birdybro/FPGA_Amp/TASKS.md

# Engineering task ledger

Last updated: 2026-08-15

## Current milestone

Advance the openly routed V1 phono core toward a stereo product-board platform
without changing the frozen reference circuit. The product architecture now
includes a separately clocked eARC/ARC TV input, touchscreen front panel,
premium physical controls, motor-follow volume, line conversion, and independent
power/protection. The Nexys Video artifact remains ready for volatile SRAM
loading; matching connected hardware and an installed open programmer are still
external blockers. Product eARC work is additionally gated by adopter/vendor
access and finished-device compliance.

## Active, highest value first

- [x] Implement the board-facing relay/XSMT sequence for the routed DAC PCB.
  Normal release asserts `LINE_RELAY_EN_CTL`, waits 491,520 fabric clocks
  (5 ms at 98.304 MHz), then asserts `DAC_SOFT_UNMUTE_CTL`; orderly mute drops
  XSMT first, waits the same conservative interval, and then opens the relays.
  Emergency mute drops both controller permissions on the next fabric edge,
  while the PCB's independent `HARD_MUTE_N` remains the asynchronous veto.
  Directed RTL covers release, orderly mute, release cancellation, and
  emergency drop. Yosys reports 28 estimated XC7 logic cells / 22 flip-flops /
  no DSP or BRAM / zero warnings. Physical relay/ramp/transient timing remains
  a bench release gate.
- [x] Integrate PCM5242 initialization, verification, and runtime health into
  one fail-low controller. The verifier cannot start before all 20 writes are
  ACKed; the first four-register runtime poll cannot start before all 24
  page/read/status checks pass; and `unmute_permitted` stays low until all 48
  transactions succeed. Periodic polls then check live/latched clock errors,
  active/sticky output shorts, DSP boot, and run state. Simulation proves
  success, ACK-only and startup-snapshot non-permission, both startup failure
  phases, and post-unmute short detection that revokes permission. Yosys reports
  340 estimated XC7 logic cells / 439 flip-flops / no DSP or BRAM / zero
  warnings. Top-level pin integration and physical fault/mute timing remain
  release gates.
- [x] Add a synthesizable one-byte-register I2C read primitive needed by the
  PCM5242 verification layer. The engine emits address+W, register, repeated
  START, address+R, one data byte, master NACK, and STOP while honoring clock
  stretching. Its bus-level regression checks all three transmitted bytes,
  returned data, released-bus completion, and fail-closed address-NACK abort.
  Yosys reports 70 estimated XC7 logic cells / 63 flip-flops / no DSP or BRAM /
  zero warnings. This primitive does not itself declare the DAC configured;
  the completed verifier/controller layers own that decision.
- [x] Implement the PCM5242 write-only reference-path bootstrap. The common I2C
  engine now supports one- or two-byte register addresses without regressing
  the ADAU1761 path. The new sequence emits twenty exact transactions at board
  address 0x4c for external SCK, 24-bit I2S, direct stereo routing, ROM
  interpolation program 1, unity digital/analog gain, VREF output, no
  de-emphasis, and disabled zero-detect auto mute. A bus model checks every
  byte, released-bus completion, and fail-closed NACK abort. Yosys reports 83
  estimated XC7 logic cells / 86 flip-flops / no DSP or BRAM / zero warnings.
  `configuration_written` is explicitly not an unmute permit; the downstream
  verifier and runtime monitor now provide the stronger controller gate.
- [x] Generate and openly route the four-layer PCM5242 DAC/line-output Rev-A
  EVT board. The 112 x 72 mm design implements 48 kHz external-clock slave I2S,
  I2C unity/reference configuration, separate analog/digital TPS7A2033
  post-regulation, official-reference 499 ohm balanced and RCA reconstruction
  branches, three normally-open fail-open signal relays, and provisional
  chassis-referenced ESD sites. Two SN74LVC1G08 gates independently require
  controller and external-supervisor permission before relay drive or PCM5242
  XSMT can assert; all permissions fail low. Rotating the DAC to face its analog
  pins toward the filters fixed the initially fragile output escapes. The open
  route has 581 segments and 86 vias; KiCad 10.0.5 reports zero ERC, zero DRC,
  and zero unconnected items. The verifier locks converter/interlock/relay pad
  maps, mode straps, filter values, DNP chassis options, loading calculations,
  stack, dimensions, and routing minima. This is not fabrication-released:
  register/readback firmware, loaded audio and mute/brownout measurements,
  connector/chassis mechanics, ESD/RF, stackup, DFM, and physical validation
  remain gates.
- [x] Generate and openly route the four-layer phono/ADC Rev-A EVT board. The
  130 x 90 mm design implements 47.5 kilohm MM loading, relay-selected
  0/47/100/147 pF capacitance, OPA1656 flat 20.008/26.064/32.002 dB gain,
  OPA1632 fully differential drive/filtering, a 48 kHz master PCM4202 with its
  reference-mode HPF disabled, local +/-12 V/+5 V/+3.3 V post-regulation,
  fail-low relay controls, separated relay power, and a chassis-bond population
  choice. The open Freerouting route has 926 segments and 141 vias; KiCad 10.0.5
  reports zero ERC, zero DRC, and zero unconnected items. A source-aware verifier
  locks pad maps, relay defaults, straps, headroom calculations, stack,
  dimensions, DNP states, and routing minima. This is not fabrication-released:
  production RCA/ground mechanics, measured capacitance/noise/hum/overload/
  crosstalk/RF/ESD, stackup review, muted switching, and the 128-fS FPGA receive
  path remain gates.
- [x] Generate and openly route the six-layer front-panel controller Rev-A EVT
  board. Its STM32H753ZIT6 allocation machine-checks 106 unique LQFP-144 I/Os
  for RGB565 LTDC, 32 MiB x16 SDRAM, 32 MiB Quad-SPI, capacitive touch, three
  panel encoders, mute/standby, digital-board control, and the motor-volume
  daughterboard. The board also implements the TPS62132 3.3 V rail, TPS61165
  nominal 60.2 mA backlight boost, MCU analog/core power, oscillators, reset,
  SWD, source damping, fail-asserted mute, and separate panel/control/motor
  harnesses. KiCad 10.0.5 reports 0 ERC, 0 DRC, and 0 unconnected items on the
  150 x 90 mm route with 1,827 segments and 327 vias. Exact project-local Molex
  54104-4031/52271-0679 footprints now reproduce the manufacturer-drawing pad
  count, pitch, land size, contact style, and fitting-nail geometry under
  regression. This is not a fabrication release: physical connector fit/FAI,
  six-layer stackup/SI and SDRAM timing, switching-supply layout, enclosure
  mechanics, sourcing, EMC, and physical validation remain gates. The pin audit
  also proves direct RMII Ethernet is unavailable in this Rev-A LQFP allocation.
- [x] Create and openly route the first KiCad EVT PCB for the motorized-volume
  subsystem. The 80 x 48 mm four-layer daughterboard implements the protected
  5 V rail, DRV8874 PH/EN bridge, hardware current regulation, IPROPI and fault
  telemetry, separate motor and dual-position connectors, ratiometric wiper
  filtering, DNP snubber site, and eight labeled test points. One source table
  generates its native schematic, PCB placement, custom symbols, and BOM;
  Freerouting v2.2.4 supplies the checked-in route through DSN/SES. KiCad 10.0.5
  reports 0 ERC, 0 DRC, and 0 unconnected items, and a source-aware verifier
  checks the DRV8874 pin map, board dimensions, stack, DNP state, connector
  isolation, minimum geometries, and reports. Gerbers, split drill files, maps,
  report, and DNP-filtered placement data regenerate with
  `make kicad-motor-fab`. This is an unbuilt motor-only EVT board; connector
  release, thermal-via strategy, motor emissions, stall thresholds, mechanism
  feel, and life qualification remain open.
- [x] Establish a comprehensive product hardware baseline for eARC, LCD/touch,
  premium physical controls, and motorized volume. The architecture partitions
  the product into digital/eARC, phono/ADC, DAC/line-output, front-panel, and
  power/protection boards so motor/display/HDMI currents are physically
  separated from the MM input. Fifty-two classified requirements and 31 signal
  rows across six board interfaces are machine checked. Mutation regressions
  reject duplicate IDs, unknown boards, untraced requirements, connector-contact
  overcommit, interface-budget drift, or downgrading the reference, stereo-PCM,
  analog-mute, and motor-out-of-audio-path invariants. This is a board
  architecture/specification result, not a released schematic, BOM, eARC
  license, compliance result, or motor-life claim.
- [x] Implement the mechanism-independent motor-volume servo core in portable
  C11. It provides soft endpoint clamping, far/approach duty, deadband/coast,
  exact reversal dead time, explicit and inferred manual takeover, hardware-
  current-feedback stall retention, travel timeout, driver/sensor faults, and a
  safe clear that adopts present position instead of retrying a stop. The first
  host run exposed and fixed a pending-reversal/manual-takeover collision; the
  failing reversal sequence is retained. The warning-as-error regression now
  passes. This does not validate PWM/ADC peripherals, motor EMI/torque/noise,
  touchscreen interaction, or mechanism lifetime.
- [x] Implement the matching stereo FPGA master-volume endpoint outside the
  historical model. Unsigned Q0.31 targets slew in at most 1,024 valid samples
  by default without division; zero and the exact-unity sentinel bypass
  multiplication, while signed stereo products retain all 64 bits and use
  symmetric round-to-nearest. Warning-free directed/randomized RTL covers
  retargeting, rounding, stereo independence, silence, unity, and invalid-target
  retention. Yosys reports 312 estimated logic cells / 151 flip-flops / eight
  DSP48E1 / no BRAM / zero problems. The primitive is not yet wired into the
  mono Nexys top, and this is no placed timing or stereo product-fit claim.
- [ ] Close eARC EVT-0 gates before a mainboard schematic: confirm the current
  supported audio-device receiver/successor and supply path; obtain HDMI adopter
  and vendor reference/API access; compare SRC4392 and AD1896 with asynchronous
  PCM; verify stereo LPCM capability exchange, ARC fallback, CEC volume, mute,
  relock, and latency on analyzer/EVM hardware. Do not advertise compressed or
  multichannel formats in V1.
- [x] Add PCM5242 page-aware register readback and startup status verification.
  Twenty-four exact operations select pages 0/1, compare every critical field
  with reserved-bit-safe masks, return to page 0, and require detected 48 kHz,
  512-fS SCK, 64-fS BCK, valid-clock flags, DSP boot, and run state. Directed
  bus simulation proves success plus masked-mismatch and NACK fail-closed paths.
  Yosys reports 170 estimated XC7 logic cells / 173 flip-flops / no DSP or BRAM /
  zero warnings. `configuration_verified` remains distinct from the earlier
  ACK-only result and is a startup snapshot; the integrated controller now
  follows it with continuous clock/short/power polling before and after unmute.
- [ ] Turn the completed front-panel controller and motor-volume EVT boards
  into a fabrication candidate: print/fit the drawing-derived Molex footprints,
  obtain assembler DFM and first-article inspection; obtain a fabricator stackup
  and run SDRAM/LTDC/clock SI; manually review and refine both switching
  converters; freeze encoder/display/enclosure geometry; select keyed production
  harnesses; then close sourcing, EMC, touch-safety, motor torque/noise/stall,
  and 100,000-cycle mechanism qualification.
- [x] Extend and verify the I2S receive boundary for the phono board's PCM4202
  master mode: 24-bit data in 64-BCK half-frames at 128-fS/6.144 MHz BCK and
  48 kHz LRCK. The receive-only block crosses complete stereo frames into
  49.152 MHz fabric through a depth-8 asynchronous FIFO so it does not force a
  future 32-BCK DAC onto the ADC clock. Both 32- and 64-BCK protocol regressions
  pass; the exact PCM4202 test passes 16 frames with unrelated phase,
  backpressure, held-valid checks, signed endpoints, and injected LRCK fault.
  Yosys reports 252 LC / 791 FF / no DSP or BRAM / zero structural problems.
  Physical FPGA-pin timing and populated-board validation remain open.
- [ ] Implement and openly route the actual stereo product hierarchy before
  freezing the production FPGA/package. The present 217-DSP mono Nexys build is
  evidence for an XC7A200T resource-class baseline, not proof that stereo plus
  TV routing, delay, diagnostics, and future full-amplifier headroom fit or meet
  timing/thermal limits.

- [x] Close the remaining 49.152 MHz complete-stream timing gap with registered
  cross-block scheduling, guided by the now-completed legal route. Circular
  histories reduce the complete 384 kHz candidate from 17,693 LC / 14,737
  packed FFX to 15,716 LC / 8,589 packed FFX. The full A200T route reaches
  48.482 MHz versus 49.152 MHz, leaving a 1.38% gap; its 20.626 ns state-to-
  tube path crosses the corrected/current voltage mux, plate-node subtraction,
  Q20 conversion, and factorized-tube input mapping. Exact acceptance/chord
  tube-pin prefetch removes that path, and a diagnostic-only four-boundary KCL
  maximum pipeline preserves all KCL/solver/stream vectors at 127 clocks, but
  the clean legal route reaches only 47.07 MHz through chord preview and tube
  conversion. Reject this pin-prefetch/deep-maximum family: another pin register
  costs a clock per correction pass and cannot fit the 127-of-128-clock
  contract. A zero-latency
  late selector now converts the current/corrected stage-one pin pairs in
  parallel and moves the mux onto the two 32-bit tube buses. It preserves the
  64-output/512-update stream exactly at 127 clocks and improves the best legal
  seed-1 route to 48.700 MHz, a remaining 0.92% miss; seed 2 routes at 45.051
  MHz and seed-3 routing was bounded after two unusually expensive iterations.
  Its critical path is now the exact KCL residual-maximum diagnostic. A new
  low-state sideband scans the nine stable rows with one comparator in eight
  clocks, matches 1,024 BE + 1,024 trapezoidal KCL vectors and the complete
  stream, and cuts the pack to 54,699 LUTX / 8,657 FFX / 4,044 CARRY4 / 207
  DSP. Its legal 14-iteration route reaches only 47.567 MHz because the
  corrected-node-to-tube path becomes critical again. Registering the six exact
  one-cycle-early chord nodes, while leaving subtraction and Q-format conversion
  in the existing preview-to-launch interval, preserves the complete stream at
  127 clocks and closes the open A200T route at 61.072 MHz against 49.152 MHz.
  Yosys measures 15,220 LC / 8,855 FF / 207 DSP / 10 RAMB18 equivalents; open
  packing measures 54,280 LUTX / 8,855 FFX / 3,979 CARRY4 / 207 DSP. The legal
  23-iteration seed-1 route has a 16.37 ns terminal-current/state path with
  6.44 ns logic and 9.94 ns routing, leaving 3.97 ns positive estimated slack.
  Seed 2 also closes in 14 iterations at 51.080 MHz with a 19.58 ns
  registered-node-to-tube path and 0.77 ns positive estimated slack.
  This is timing closure under nextpnr's experimental `DEFAULT` grade, not
  qualified XC7A200T-1 signoff or hardware validation; bitstream generation is
  verified separately below.
  Do not replicate the prior four-boundary implementation, whose 1,076 added
  registers made routing pathological. A
  broad 123-clock parallel/pipelined profile remains exact but
  grows to 242 DSP / 66,658 packed LUTX and places at only 39.62 MHz, so do not
  promote it. Lower resource occupancy or nominal cycle margin alone is not
  timing closure.
- [ ] Complete physical implementation evidence for the selected A200T timing
  profile. The seed-1/seed-2 routes are retained, and a new fully open
  Project-X-Ray conversion now reproducibly turns the selected 44,258,864-byte
  FASM into 20,230 frame records and a 9,730,907-byte `.bit`. Two conversions
  produce the same SHA-256 (`98a53adf...2b9dcb`) after repository-relative
  source metadata and a fixed epoch timestamp; `bitread -C` validates 24,060
  configuration frames / 2,432,650 words. Run the physical oscillator/signature
  smoke test when matching hardware is available. Keep the experimental
  `DEFAULT` timing estimate distinct from qualified speed-grade and board
  measurements.
- [x] Implement and openly route the exact Nexys Video audio-clock source.
  Cascade two XC7 MMCMs from the real R4 100 MHz oscillator to 12.288 MHz
  codec MCLK and 49.152 MHz fabric clocks, with exact 960/614.4 MHz VCOs.
  Check the ratios and 128 fabric clocks per 384 kHz sample from RTL in Python.
  With an explicit 10 ns input constraint, nextpnr derives both generated
  domains and completes routing in three iterations; the 24-bit activity
  counter reaches 291.55 MHz against its correct 49.152 MHz constraint under
  the experimental `DEFAULT` grade. Pack use is 99 LUTX / 24 FFX / 6 CARRY4 /
  2 BUFG / 2 MMCM. The open Project-X-Ray stage emits a CRC-readable
  9,730,853-byte bitstream at SHA-256 `1d7d934f...234b248`. The arithmetic
  contract also checks that physical G4 `CPU_RESETN` is inverted before the
  active-high MMCM reset; this fixes and supersedes the prior
  `941a8c07...e0ff656` artifact, whose reset polarity was wrong. This is a
  clock-only harness, not hardware frequency measurement or codec operation.
- [x] Implement the board serial-clock and reset-release leaf. Divide the exact
  49.152 MHz fabric clock by 16 to 3.072 MHz BCLK, promote only this external
  interface clock through an XC7 BUFG, and keep sample processing on the fabric
  clock plus enables. Assert fabric/I2S resets asynchronously but release them
  through separate three-edge owning-domain synchronizers. A warning-free RTL
  test checks exact 16-clock periods, release latency, and asynchronous
  reassertion. Yosys reports 10 FDCE / 1 CARRY4 / 1 BUFG, zero problems, and no
  warnings. Full named-board timing awaits composition with the pin top.
- [x] Implement the device-neutral open-drain I2C register-write primitive for
  codec startup. It transmits the seven-bit device address, 16-bit register
  address, and one data byte, honors SCL clock stretching, samples every ACK,
  and completes with a STOP after either ACK or NACK. A directed bus-target
  test checks exact bytes, a deliberate address-byte NACK, and recovery on the
  next write. Warning-free Yosys XC7 synthesis reports 43 estimated logic
  cells, 59 flip-flops, three CARRY4s, and no DSP or BRAM. Reads, arbitration,
  multi-main operation, and codec register readback remain explicitly out of
  scope.
- [x] Add and verify the ADAU1761-specific fail-closed startup sequence. Keep
  the codec subordinate to FPGA-supplied BCLK/LRCLK, configure direct 12.288
  MHz MCLK for the 48 kHz family, leave the line outputs muted until the last
  writes, and abort before later writes on any NACK. The bus-target regression
  checks all 27 address/register/data transactions and then injects a NACK at
  table index five, where the sequencer exposes the failure and emits no more
  writes. Warning-free Yosys XC7 synthesis reports 88 estimated logic cells,
  94 flip-flops, ten CARRY4s, and no DSP/BRAM. Physical ACKs and analog output
  behavior remain unmeasured.
- [x] Compose and structurally verify the actual Nexys Video pin top: the exact
  clock leaf, reset/BCLK leaf, codec initializer, single shared LRCLK,
  bidirectional serial audio, calibrated 384 kHz phono hierarchy, SPI control,
  forced-zero startup data, and status indicators. A mutation-tested contract
  checks 18 physical pin/IO-standard pairs, active-low reset, open-drain I2C,
  the internal 3.072 MHz BCLK constraint, the selected 384 kHz schedule, and
  fail-closed release. The shared-I2S guard regression proves zero DAC data and
  a held serial-transport reset until two synchronized ready edges, preventing
  undefined pre-bootstrap ADC frames from filling the receive FIFO. Complete
  Yosys synthesis reports 16,688
  LC / 11,687 FF / 217 DSP / ten RAMB18 equivalents with zero structural
  problems; open packing uses 59,710 LUTX / 11,687 FFX / 4,192 CARRY4. This is
  composition/fit evidence, not a hardware-ready claim.
- [x] Complete and retain the full board route, then generate and CRC-check its
  Project-X-Ray bitstream. Both generated domains and the otherwise-uninferrable
  fabric-divided BCLK carry explicit constraints. Static placement estimates
  only 41.03 MHz, but router2 reaches zero overuse in 20 iterations and passes
  at 54.663 MHz against 49.152 MHz fabric plus 123.457 MHz against 3.072 MHz
  BCLK under the experimental `DEFAULT` grade. The 56,556,532-byte routed FASM
  converts to 20,230 frame records and a 9,730,825-byte `.bit`; two conversions
  are identical at SHA-256 `5f196e52...b09dbb8`, and `bitread -C` accepts
  24,060 frames / 2,432,650 words. The result is neither qualified -1 timing
  nor a hardware validation claim; the image remains unprogrammed.
- [ ] Program the complete image on a matching Nexys Video and validate reset,
  12.288 MHz MCLK, 3.072 MHz BCLK, 48 kHz LRCLK, all codec I2C ACKs, startup
  silence, line-output audio, and SPI diagnostics with external instruments.
  The non-programming preflight now validates the exact part, byte count,
  SHA-256, CRC evidence, frame count, and word count before using the official
  openFPGALoader `nexysVideo` detection profile. It passes the artifact but the
  2026-08-15 host has neither openFPGALoader nor a Nexys Video USB device, so
  no configuration was attempted. `nexys-audio-program-sram` is deliberately
  volatile-only and requires successful detection first. Do not infer any of
  these physical results from the CRC-readable artifact.
- [x] Carry the timing-closed 384 kHz / 49.152 MHz profile into the actual
  fabric adapter and complete SPI-controlled I²S hierarchy. Preserve 768 kHz
  as the default, add explicit rate-selectable vector/test runners, and pass
  exact adapter, serial I²S, register-control, and 15-frame SPI regressions.
  The 384 kHz pin test accepts all 64 serial inputs, matches 44 observable DAC
  frames, keeps each local FIFO high-water mark at one, and measures 265 fabric
  clocks from model input to output-valid plus the unchanged 192-BCLK/three-
  sample frame-boundary latency. Yosys reports 15,699 LC / 9,085 FF for the
  adapter and 16,614 LC / 11,586 FF for the full SPI/I²S top, both with
  217 DSP / 10 RAMB18 equivalents and zero structural-check problems. A board
  top now has a real, openly routed 49.152 MHz/12.288 MHz clock source. It
  is now composed with the codec's physical shared LRCLK, deterministic reset
  release, and byte-tested ADAU1761 initialization in the board wrapper. Full
  board routing and all physical codec/audio behavior remain unvalidated; do
  not label the clock-only image or structural board top as hardware-ready.
- [ ] Isolate and reduce the remaining fixed circuit/state/chord error. With
  the implemented 1,024-point grid branch, raw final-window error is now
  0.372/0.291 mV at 1.0 V and 0.631/0.321 mV at 1.5 V for backward Euler/
  trapezoidal. A continuous-coefficient fixed-interface A/B bounds integer tube
  evaluation to <=0.168 mV burst RMS and identifies circuit/state/chord as the
  6.40--19.07 mV dominant burst layer. The implemented terminal correction
  cuts 1.0/1.5 V burst RMS to 4.895/6.817 mV for backward Euler and
  4.709/3.604 mV for trapezoidal at 127 clocks. Held-bank reselection,
  rational terminal relaxation, full dual-triode operating points, and
  stage-one-split banks all fail cross-level/recovery acceptance. Further
  contraction now requires a different solver formulation or additional
  schedule margin; do not tune the frozen circuit or accept a one-level fit.
- [ ] Prove 98.304 MHz named-part timing for the 127-clock trapezoidal terminal
  stream. Current controlled generic synthesis fits XC7A100T structurally at
  18,280 LC / 206 of
  240 DSP48E1 / 8 RAMB18E1 + 1 RAMB36E1, but the parallel terminal-current path and one-clock
  sample margin require the open Yosys/nextpnr-Himbaechel place/route flow
  before hardware selection. Project X-Ray contains the exact
  `xc7a100tcsg324-1` part, but the current experimental backend uses a single
  `DEFAULT` timing grade, so routing evidence and qualified -1 speed-grade
  signoff must remain distinct. The first full-solver harness packs at 50,789
  `SLICE_LUTX` / 174 DSP and reaches only 13.90 MHz after placement. A
  value-only tube substitution places at 13.67 MHz, falsifying the hypothesis
  that Hermite is the dominant whole-solver limiter. A standalone bit-exact
  iterative Hermite replacement now
  closes post-route at 132.54 MHz with two DSPs and three-clock latency, but
  inserting that latency into all three dependent tube functions would exceed
  the current 127-clock solver budget. The separately named value-only linear
  candidate instead retains eight clocks: 100,000-point error is 47.49 nA
  worst, tube and complete terminal solver RTL are bit-exact, and the isolated
  tube routes at 113.24 MHz. Its full harness packs at 49,530 `SLICE_LUTX`, 166
  DSP, 13 RAMB18E1, and 5 RAMB36E1. The isolated 54-DSP terminal-current block
  improves from 51.95 to 88.83 MHz when its exact overflow count is balanced,
  but still misses 98.304 MHz. Isolated chord routes at 46.40 MHz and isolated
  KCL routes at 16.64 MHz, with KCL's accumulator-to-global-fallback cone
  matching the whole-solver failure. A bit-exact residual staging register and
  balanced KCL reductions retain the 127-clock integrated contract and improve
  KCL placement to 33.92 MHz. Parallel evaluation of the two physical tube
  sections is bit-exact at 84/95 clocks and fits structurally at 209/240 DSPs.
  The recovered margin now funds two KCL column-fill clocks, two KCL finish
  clocks, and two chord-apply clocks per pass: the complete solver is exact at
  119 clocks and the chord route closes at 100.92 MHz. A legal 42.07 MHz KCL
  route instead identified the exact maximum diagnostic as the limiter.
  Accumulator and final-only maximum pipelines plus exact sign-extension fit
  tests now produce a bit-exact 126-clock complete schedule and raise the
  isolated KCL to 92.23 MHz post-route. Close the remaining 6.6% KCL gap and
  resolve the full-hierarchy congestion: the 14,990-LC design packs to 59,027
  slice LUT elements / 209 DSPs but places at only 34.20 MHz. Region analysis
  shows KCL and terminal-current spanning nearly all DSP rows while the two
  tube engines and chord occupy separated hard-block regions. The same netlist
  uses only 209/740 DSPs on XC7A200T, but seed/default placement reaches 23.83
  MHz, a second seed reaches 30.55 MHz, and timing-weight-20 reaches only 35.22
  MHz. Capacity alone is therefore rejected as the fix. A selectable two-batch
  terminal-current schedule now proves 1,027 standalone and 512 integrated
  vectors exact at 127 clocks, cuts DSP use from 209 to 189, and routes its
  isolated block at 90.50 MHz with the default weight and 99.59 MHz with timing
  weight 20, closing that block's constraint. The complete hierarchy
  nevertheless places at only 25.02 MHz with 59,514 LUTX / 14,590 FFX, worse
  than baseline. Timing weight 20 raises the complete candidate only to 32.56
  MHz and disperses its 34 terminal DSPs across a 91-by-167 coordinate region;
  it remains slower than the selected baseline's 34.20 MHz. Resource sharing
  in one block and placer-weight tuning are therefore both insufficient. An
  overlapping hierarchy floorplan improves the candidate to 36.83 MHz by
  reserving left/center DSP columns for KCL/RHS and center/right columns for
  nonlinear blocks, but still misses by 2.67x. Mapping all eleven KCL
  multipliers to LUT logic is legal but grows the complete candidate to
  101,479/126,800 packed LUT elements while reducing DSPs to 117; the isolated
  71,592-LUT block does not complete analytical placement in a useful interval,
  so no Fmax is claimed. Softening only the two capacitor multipliers reduces
  the full design to 171 DSPs at 66,341 LUTX, but the isolated KCL places at
  only 37.57 MHz and is also rejected. Decoupling the final-only exact maximum
  diagnostic recovers a bit-exact 123-clock schedule and five-clock margin.
  Acceptance-edge branch-9 prefetch now spends none of that margin while
  sharing the two KCL capacitor products: isolated/full DSP use falls from
  72/209 to 63/200, but placement reaches only 72.95/35.06 MHz and a weight-20
  full placement falls to 29.05 MHz. Composing this with terminal-current
  sharing produces an exact 124-clock, 180-DSP solver, but default and
  floorplanned placements reach only 30.63/32.94 MHz. Develop a broader
  cross-block time-multiplexed schedule with registered multiplier boundaries;
  do not treat lower DSP occupancy by itself as evidence of timing progress.
  A separately labeled 384 kHz/8x study now bounds 10/20 kHz SPICE error at
  0.06653 dB / 0.02234 degree and finds complete-circuit selected products
  within 0.52 dB of 768 kHz through steady 0.5 V, while exposing an 11.33 dB
  static-tube stress penalty at -118.65 dBc. Its 256-cycle budget is promising,
  but reference mode remains 16x. Distinct 384 kHz fixed assets and the
  nonlinear RTL core are now exact across 1,024 all-bank chord, 1,024 KCL, and
  512 persistent solver vectors at 10/11/127 clocks with zero solver diagnostics. The 19-bit chord bank
  costs nine more DSPs than the controlled 768 kHz core synthesis. The complete
  48→384→48 kHz candidate is now exact for 64 external outputs / 512
  nonlinear updates with zero diagnostics. After serial center-tap sharing and
  reset-masked circular resampler histories, full-stream synthesis is 15,716
  LC / 8,547 FF / 207 DSP / 10 RAMB18 equivalents at 384 kHz and 16,062 / 9,033
  / 206 / 10 at 768 kHz. The
  772,608-update fixed transient comparison is diagnostic-clean and finds only
  +0.1875 ms recovery delta / -84.71 dB aligned recovery error. Known-delay
  windowed-sinc alignment measures the pop at -35.92 dB overall / 2.623 mV
  peak / -53.33 dB in-band; this supersedes a flawed linear-interpolation
  result. Converter/float/fixed in-band decomposition is -67.49/-55.71/-53.33
  dB. Long-vector RTL proves both
  rate-specific implementations exact for 24,576 outputs / 294,912 nonlinear
  updates. The matched absolute pop-response comparison now measures -61.47 dB
  residual / 0.539 mV maximum at the 384 kHz path's 48 kHz output versus
  -61.00 dB / 0.546 mV for 768 kHz, without latency, gain, or DC fitting and
  with zero failed solves. Thus this transient does not favor 16x. The complete
  harness packs on A100T but heap placement fails legalization; a legal A200T
  static placement reaches only 34.40 MHz against 98.304 MHz. An explicit
  49.152 MHz schedule is exact with one clock of solver margin and improves
  static placement to 38.34 MHz against 49.152 MHz, but still misses by 1.28x.
  Circular decimator history removes 4,173 packed FFX and makes heap placement
  legal for the first time, although its 22.79 MHz estimate still fails the
  clock. Circular interpolation then improves static placement to 41.27 MHz
  while preserving every stream output. Reference mode remains 16x and broader
  registered scheduling is required.

## Completed this milestone

- [x] Implement and route exact tube-pin prefetch plus diagnostic-only KCL
  maximum retiming without changing the 127-clock solver schedule. Match 1,024
  backward-Euler KCL, 1,024 rate-specific trapezoidal KCL, 512 persistent
  solver, and 64-output/512-update complete-stream vectors. Remove the
  invalid-only combinational maximum load identified by route. Measure 15,852
  LC / 9,793 FF / 207 DSP / 10 RAMB18 equivalents and a legal 47.07 MHz A200T
  route with a 21.24 ns chord-preview/tube-input path. Reject the candidate as
  slower than the selected 48.482 MHz baseline.

- [x] Route the circular-resampler 49.152 MHz complete-stream harness legally
  on XC7A200T. Measure 48.482 MHz post-route, a 1.38% miss, with 56,041 LUTX /
  8,589 FFX / 4,116 CARRY4 / 207 DSP and a 20.626 ns state/voltage/tube-input
  critical path. Preserve the generated FASM only as implementation evidence;
  do not claim a bitstream or hardware readiness. Compose and reject a broader
  exact 123-clock profile after its 66,658-LUTX / 242-DSP A200T placement
  reaches only 39.62 MHz.

- [x] Replace reset-cleared half-band interpolator shift registers with reset-
  masked circular distributed memories using one multiplexed asynchronous read
  port for MAC and pre-write odd-phase capture. Add a reset-after-history test
  for both output phases and preserve all unit, 8x/16x converter, and complete
  stream vectors exactly. Measure 364 LC / 306 FF / 4 DSP for one stage, 950 /
  938 / 12 for 8x, and 1,417 / 1,229 / 16 for 16x. Reduce complete 384/768 kHz
  synthesis to 15,716 / 16,062 LC and static A200T placement to 56,041 LUTX /
  8,589 FFX / 4,116 CARRY4 / 207 DSP at 41.27 MHz versus 49.152 MHz.

- [x] Replace reset-cleared half-band decimator shift registers with a
  reset-masked circular distributed-memory history. Mask retained memory using
  an explicit valid-sample count, add a post-history reset regression, and
  preserve every unit, 8x/16x converter, and complete 384/768 kHz stream output
  exactly. Measure 349 LC / 214 FF / 4 DSP for one 79-tap stage, 961 / 618 / 12
  for 8x, and 1,408 / 817 / 16 for 16x. Reduce the complete 384 kHz stream to
  16,315 LC / 10,520 FF / 207 DSP and prove legal A200T heap placement at
  58,363 packed LUTX / 10,562 FFX, while retaining its failed 22.79 MHz timing
  result and the static placer's still-failing 38.38 MHz result, then skip
  routing. The refreshed static hierarchy is 2,725 LUTX / 618 FFX / 12 DSP for
  the decimator versus the prior 8,397 / 4,791 / 12.

- [x] Extend the placed-JSON hierarchy analyzer to distinguish the complete
  8x interpolator and decimator, with regression coverage for flattened names.
  Measure decimator/interpolator/KCL placement at 8,397/5,193/19,609 LUTX,
  4,791/2,910/2,920 FFX, and 244x143/244x139/190x185 coordinate spans.

- [x] Implement and verify a half-frequency fabric schedule for the 384 kHz
  candidate without changing circuit arithmetic. Match both 1,024-output
  interpolator schedules and all 64 complete outputs / 512 nonlinear updates
  exactly at 49.152 MHz with zero diagnostics and a 127-of-128-clock solver.
  Place the complete A200T static design at 38.34 MHz versus 49.152 MHz and
  retain the reduced-netlist heap legalization failure; do not claim routing.

- [x] Serialize the half-band decimator center tap through the existing MAC.
  Preserve the pre-shift history operand explicitly and match 256 unit, both
  8x/16x chain, and both complete nonlinear-stream regressions exactly. Reduce
  decimator synthesis from 24 to 12 DSPs at 8x and from 32 to 16 at 16x; update
  complete synthesis to 17,693 LC / 207 DSP and 18,280 / 206 respectively.

- [x] Add a complete 384 kHz three-pin timing harness and open-tool placement
  path. Pack it on XC7A100T at 63,902 LUTX / 14,737 FFX / 4,071 CARRY4 / 207
  DSP; retain the failed heap legalization. Legally place the same netlist on
  XC7A200T with the static placer and measure 34.40 MHz versus 98.304 MHz, then
  skip routing after the 2.86x miss.

- [x] Compare both floating rate-specific pop/control responses directly with
  ngspice driven at the ideal INPUT node. Use matched interpolation and
  decimation, 180,000--360,000 raw SPICE points per run, and no alignment or
  gain fitting. Measure -61.47/-61.00 dB external residual and 0.539/0.546 mV
  maximum error at 384/768 kHz, with zero failed Newton solves.

- [x] Correct the transient A/B alignment error. Add optional caller-known
  latency and 64-tap Lanczos-windowed sinc interpolation to the null tool, with
  a three-tone upper-band regression below -70 dB. Re-run 772,608 fixed updates
  and a 393,216-update converter/float/fixed decomposition. Supersede the
  invalid -15.18 dB / 85.6 mV pop claim with -35.92 dB overall / 2.623 mV peak /
  -53.33 dB in-band; measure recovery at -84.71 dB overall.

- [x] Capture the rate-study transients directly from both complete RTL paths.
  Match 4,096 pop plus 8,192 overload/recovery outputs at each rate: 24,576
  Q8.24 outputs / 294,912 nonlinear updates are fixed-exact with zero
  diagnostics at 127 clocks. Bound maximum solver residual to 0.672 uA at
  384 kHz and 0.322 uA at 768 kHz; retain the separate failing rate A/B.

- [x] Compare complete 384/768 kHz fixed streams on matched record-pop and
  accepted-range 0.5 V overload/control trajectories. Process 772,608 nonlinear
  updates with zero diagnostics; measure 147.771/147.583 ms recovery. The
  original linear-interpolation null was later corrected by the explicit
  known-delay/windowed-sinc milestone above.

- [x] Compose the exact three-stage converters with the rate-specific 384 kHz
  banked-terminal core. Generalize the bit-accurate stream model and vector/
  RTL runners without changing the 768 kHz default; match 64 outputs across
  512 persistent nonlinear updates with zero converter, solver, or deadline
  diagnostics. The initial controlled Yosys structures were 17,629 LC / 219 DSP
  / 10 RAMB18 equivalents for 384 kHz and 18,302 / 222 / 10 for 768 kHz;
  center-tap multiplier sharing supersedes those resource values above.

- [x] Implement an explicit three-stage 48↔384 kHz converter without changing
  the four-stage reference modules. Match 1,024 interpolation and 128
  decimation Q8.24 RTL outputs exactly with zero saturation, overrun, or input-
  phase errors; measure eight internal samples / 20.83 µs of interpolation
  scheduling delay. The initial decimator was 2,355 LC / 24 DSP; the later
  bit-exact center-tap sharing milestone supersedes it with 2,448 / 12.

- [x] Generate a distinct 384 kHz trapezoidal fixed-point asset set and make
  its numerical differences explicit. Widen the Q17.1 chord bank from signed
  18 to 19 bits for its measured -23,414..+146,717 range; preserve exact
  product width/sign extension. Match 1,024 all-bank chord, 1,024 KCL, and 512
  persistent full-solver RTL vectors at 10/11/127 clocks with zero solver diagnostics. Synthesize the
  complete core using Yosys at 13,713 LC / 183 DSP / 10 RAMB18 equivalents,
  versus a controlled 13,158 / 174 / 10 build at 768 kHz; make no Fmax or
  reference-mode promotion claim.

- [x] Quantify an explicit 8x internal-rate architecture without changing the
  16x reference. Extend the reproducible SPICE study to 384 kHz trapezoidal,
  add static-Koren and complete-circuit 8x/16x nonlinear product comparisons at
  20 kHz, and retain exact 10 ms coherent analysis windows. Measure -0.058 dB
  complete-circuit fundamental change, <=0.52 dB selected-product change
  through steady 0.5 V, and the separate -118.65 dBc static-tube stress result.
  Record the remaining fixed/RTL/transient verification debt rather than
  silently reducing oversampling.

- [x] Reuse the two KCL capacitor products through one explicit 48-by-44-bit
  multiplier. Prefetch branch 9 on the accepting edge so 1,024 vectors per
  integration method remain exact at 16 clocks and the 512-vector complete
  solver stays exact at 123 clocks. Measure 63 isolated and 200 complete DSPs,
  but only 72.95 and 35.06 MHz placement. Compose with terminal-current sharing
  at 124 clocks / 180 DSPs and measure only 30.63 MHz default and 32.94 MHz
  floorplanned placement. Retain the exact area option while rejecting it as
  the selected timing architecture.

- [x] Decouple the final-only exact KCL maximum diagnostic from the correction
  result consumed by chord. Verify 1,024 vectors per integration method and 512
  stateful solver vectors bit-exact; reduce correction latency from 19 to 16
  clocks and the full solver from 126 to 123. Measure a legal 87.07 MHz isolated
  route, an 80.03 MHz timing-weight-20 placement, and a 31.97 MHz full placement
  at 209 DSPs. Retain the recovered five-clock schedule margin while rejecting
  diagnostic decoupling itself as an Fmax or congestion fix.

- [x] Add an exact open-XC7 pack-only measurement stage and evaluate mapping
  all eleven KCL multipliers to LUT logic. Assert the multiplier selection in
  Yosys before remapping; measure isolated 71,592 LUTX / 0 DSP and complete
  101,479 LUTX / 117 DSP packing. Stop two non-convergent exploratory
  placements without claiming timing, retain normal pack summaries, and reject
  the all-soft mapping as the current A100T implementation.

- [x] Measure a narrower soft-multiplier split. Assert selection of only the
  two 48x44 capacitor multipliers while retaining nine DSP-backed matrix
  multipliers. Record 36,327 LUTX / 54 DSP and 37.57 MHz for isolated seed-2
  placement, versus the selected 72-DSP KCL's 92.23 MHz route; pack the full
  hierarchy at 66,341 LUTX / 171 DSP and reject further implementation work on
  an unpipelined soft-multiply branch.

- [x] Implement and measure two-batch terminal-current resource sharing. Use
  fixed lane-pair muxes to avoid synthesis-created variable-index trees, pass
  1,027 exact block vectors and 512 complete stateful vectors, and retain the
  exact 127-clock deadline. Measure 34 rather than 54 isolated DSPs, 90.50 MHz
  with the default placement weight, and 99.59 MHz with timing weight 20. Then
  measure the complete 189-DSP hierarchy at only 25.02 MHz placement. Keep the
  implementation selectable and reject it as the default full-solver timing
  fix rather than reporting an isolated-only resource/timing win.

- [x] Preserve open-XC7 tuning experiments with validated, filesystem-safe run
  tags. Reproduce the isolated timing-weight-20 closure in its own artifact
  directory, then place the complete shared-terminal solver at the same weight.
  Measure only 32.56 MHz versus the 98.304 MHz target and retain the default
  25.02 MHz evidence separately.

- [x] Add and measure a nextpnr pre-place hierarchy floorplan. Reject a strict
  76-of-80-DSP left partition after it fails to complete a first heap iteration;
  retain overlapping two-column regions with 80 sites of slack per group.
  Measure 36.83 MHz, 13.1% above the unconstrained weight-20 candidate but still
  2.67x short, and skip routing.

- [x] Extend the pinned nextpnr-Himbaechel bootstrap and device-qualified runner
  to XC7A200T, add a Nexys Video timing-only harness, and place the unchanged
  complete solver. Measure 28% DSP and 21% packed-LUT occupancy, then test two
  seeds and a doubled heap timing weight. The best 35.22 MHz estimate remains
  2.79x short, so skip routing and reject larger-device capacity alone rather
  than claiming the 209/740-DSP fit solves timing.

- [x] Add a placement-only open-XC7 stage that emits separate placed netlist,
  log, report, and summary artifacts without claiming routing. Add a flattened
  placed-JSON hierarchy analyzer. Reproduce the complete 126-clock candidate at
  34.20 MHz placement with 59,027 LUTX / 13,458 FFX / 4,036 CARRY4 / 209 DSP /
  20 RAMB18 equivalents, then stop before routing because the miss is 2.87x.
  Quantify the KCL/terminal/tube/chord hard-block dispersion instead of
  extrapolating the isolated 92.23 MHz KCL result.

- [x] Use legal route evidence to pipeline the KCL accumulator and only the
  consumed final maximum-residual diagnostic. Preserve 1,024 vectors in each
  integration mode and 512 complete stateful vectors, including all 48 format
  fallbacks and 18 correction saturations. Replace generic signed-25 bounds
  compares with the exact sign-extension predicate; improve isolated KCL
  post-route timing from 42.07 through 64.90/72.31 to 92.23 MHz. Measure the
  complete exact schedule at 126 clocks and 14,990 LC / 13,458 FF / 209 DSP /
  20 RAMB18 equivalents without claiming full-hierarchy closure.

- [x] Add selectable bit-exact timing boundaries to the KCL column/finish and
  chord apply paths. Preserve 1,024 vectors in each KCL integration mode, 1,024
  chord vectors, the unchanged default latencies, and 512 complete stateful
  terminal vectors. Measure the combined schedule at 119 clocks, the chord at
  100.92 MHz post-route, and the KCL at only 38.95 MHz after placement. Record
  the remaining KCL miss instead of claiming whole-solver closure.

- [x] Add a selectable parallel dual-triode schedule without changing either
  physical operating point or arithmetic. Preserve 512-vector backward-Euler
  and complete trapezoidal/banked/terminal state and diagnostics exactly;
  reduce measured latency from 116/127 to 84/95 clocks. Add a named open-flow
  harness and measure 15,887 LC / 7,360 FF / 209 DSP / 20 RAMB18-equivalents,
  leaving 31 DSPs and 33 clocks per internal sample for timing work.
- [x] Isolate the actual network timing hierarchy. Measure chord correction at
  46.40 MHz and the original KCL engine at 16.64 MHz post-route. Capture
  capacitor 9 early, stage the final residual in the existing second-tube wait
  window, and balance cross-row fit/max/saturation reductions. Preserve 1,024
  backward-Euler, 1,024 trapezoidal, and 512 terminal-solver exact vectors;
  retain 127 integrated clocks while improving KCL placement to 33.92 MHz.
- [x] Factor the ten terminal trapezoidal current recomputations into a
  bit-exact timing unit, preserve both 512-vector solver regressions at 116/127
  clocks, and add named-part terminal/KCL/chord harnesses. Measure 54 DSPs and
  51.95 MHz for the original serial overflow count, replace it with an exact
  balanced popcount, and improve isolated post-route timing to 88.83 MHz.

- [x] Implement and independently label the value-only factorized timing
  candidate. Reproduce its 1,024/8,192/4,096 tables; measure 47.49 nA worst
  static current error; pass 4,110 tube, 512 wide-solver, and 512 complete
  terminal-solver vectors at unchanged latency; compare five circuit levels
  against Hermite and analytical full Newton; route the isolated tube at
  113.24 MHz. Do not promote it until the complete route is measured.
- [x] Break the three-dependent-multiply cubic-Hermite path into a reusable,
  bit-exact iterative kernel. Verify 4,096 full-range vectors, reset, and a
  start-while-busy transition; preserve all 4,110 factorized-tube vectors;
  measure 265 LC / 2 DSP structurally and 132.54 MHz after named-part routing.
  Keep its experimental `DEFAULT` timing grade and unintegrated cycle cost
  explicit.
- [x] Bound the oversampled SPI transport under arbitrary asynchronous raw-pin,
  response, and clear activity. Prove 11 synchronizer, bit-count, request,
  response-state, saturating-frame-count, frame-reset, and sticky-precedence
  properties through 32 fabric clocks; separately reach request decode,
  short-frame, and response-underflow paths in 100 steps. Keep the eight-frame
  directed integration as byte-order/full-frame evidence and do not claim
  unbounded induction or a placed SCLK limit.
- [x] Exhaustively prove converter-boundary arithmetic/control safety. Cover
  the valid positive input-coefficient range before the explicit signed-32
  cast, exact registered valid/output/hold behavior, output PCM endpoint
  saturation, and both saturating counters/sticky-clear transitions in 12
  assertions under arbitrary full-width samples and coefficients. Close Yosys
  SAT temporal induction at depth 2 and reach endpoint, saturation, and both
  invalid-configuration paths without replacing the Python bit-exact vectors.
- [x] Bound the asynchronous BCLK-rate monitor that drives the modern
  fail-closed mute guard. In a reduced four-clock/two-window instance, prove 16
  exact BCLK binary/Gray, synchronizer, window, delta, lock/drop, saturation,
  and sticky-clear properties for every 32-step arbitrary-clock interleaving.
  Reach lock followed by a retained bad-rate state in 48 steps. Keep physical
  clock accuracy, synchronizer placement/metastability, stopped-clock liveness,
  and the production 1,024-edge ratio as separately verified claims.
- [x] Bound the low-rate diagnostic-clear toggle CDC under arbitrary clock
  levels and a protocol assumption that the preceding event is observed before
  another launches. Prove ten exact pipeline, pulse-width, outstanding-event,
  no-fabrication, and accounting properties through 40 global steps; reach two
  delivered events. Add directed evidence that destination reset with an odd
  retained source toggle replays the idempotent command, and document that this
  primitive is not a reset-independent or arbitrary-rate event channel.
- [x] Bound the coherent held-bus CDC snapshot under arbitrary source and
  destination clock levels after disciplined shared startup reset. Prove nine
  capture provenance, hold stability, exact-data, valid-pulse, accounting, and
  idle properties through 40 global steps, then find a nonzero complete-transfer
  witness. Keep the result explicitly bounded and retain the directed
  destination-reset-during-request RTL test because mid-transaction reset is
  outside the formal environment.
- [x] Formally prove deterministic frame scheduling under arbitrary source
  validity/data and diagnostic clear. Use nine assertions for phase wrap,
  ready/valid/present launch strobes, accepted data, zero fill, and the exact
  saturating 32-bit underflow transition. Close Yosys 0.66 SAT temporal
  induction at depth 2 and reach an absent boundary followed by a present one.
- [x] Formally prove the atomic converter-calibration guard. Under arbitrary
  candidates, valid, mute, and clear inputs after reset, require exact
  acknowledge, simultaneous pair commit, rejection immutability, sticky
  accumulation, and clear precedence in 12 assertions. Close Yosys 0.66 SAT
  temporal induction at depth 2 and find one invalid-reject/commit/unsafe-reject
  witness. This covers the guard, not the upstream host transport.
- [x] Add a sound bounded multi-clock formal environment around the asynchronous
  FIFO. After a shared reset asserted on local edges and released while clocks
  are low, leave both clock levels and all controls arbitrary. Prove 13 Gray,
  blocked-pointer, occupancy/watermark, valid, and sticky-fault properties for
  every 32-step interleaving; separately reach depth four and both illegal-side
  stickies in 24 steps. Keep unbounded induction explicitly open because the
  current invariant set does not close it.
- [x] Formally verify the single-clock modern output mute/ramp control contract.
  With arbitrary post-reset data and controls, prove 15 reset, force-clamp,
  valid, hold, exact gain-transition, endpoint, monotonicity, and status
  assertions by Yosys 0.66 SAT temporal induction at depth 2. Separately find a
  non-vacuous witness reaching unity gain after four accepted samples. Package
  both checks as `make formal-mute`; the result does not claim CDC or analog
  speaker-safety coverage.
- [x] Integrate coherent I²S-domain FIFO diagnostics into the atomic register
  snapshot. Delay image/sequence commit until the held-bus CDC returns, expose
  busy/available status, pack RX/TX level and high-water nibbles at `0x35`, and
  make a 131,072-clock timeout retain the old image/sequence with sticky
  evidence. Prove normal capture, busy rejection, stopped-BCLK timeout,
  recovery/re-arm, timeout snapshot, and explicit clear; update the host client
  to poll completion and reject stale sequence results. Bump the compatible ABI
  minor to 1.1. Current structural synthesis is 354 LC / 735 FF for the register
  bank, 19,616 LC / 18,684 FF for the controlled hierarchy, and 19,719 LC /
  18,856 FF with SPI; the complete variants retain 216 DSP48E1 /
  8 RAMB18E1 + 1 RAMB36E1 and zero structural-check problems.
- [x] Implement the held-bus CDC primitive needed for coherent I²S-domain
  occupancy snapshots. Use a four-phase request/acknowledge protocol, hold all
  16 bits through two synchronizer stages plus a settling clock, re-arm safely,
  and survive destination reset during an active request. Prove three exact
  captures warning-free and synthesize to 5 LC / 75 FF / no DSP or RAM. The
  register transaction integration is recorded above.
- [x] Define the host-side SPI/register ABI in dependency-free Python. Encode
  exact ten-byte full-duplex frames, validate identity/version/capabilities and
  response status, require explicit mute ownership for snapshot/clear commands,
  and guard calibration commit/poll/sequence checks. Cover exact wire bytes,
  malformed/error responses, accepted/rejected calibration, and invalid host
  preconditions with six deterministic tests. A physical adapter backend remains
  a board task rather than part of the protocol contract.
- [x] Convert the measured BCLK-rate status into a fail-closed modern output
  policy at the register-controlled wrapper. Hold the immediate mute through
  three-window startup qualification, reassert it on stopped BCLK, retain it
  through clock reacquisition, snapshot the evidence, and release only after an
  explicit host clear reaches both fabric and I²S domains. Keep model scheduling
  active so startup qualification cannot overflow the receive FIFO. Updated
  later structural synthesis is 19,616 LC / 18,684 FF for the controlled
  hierarchy and 19,719 LC / 18,856 FF with SPI, both retaining 216 DSP48E1 /
  8 RAMB18E1 + 1 RAMB36E1 and zero structural-check problems.
- [x] Compose the SPI transport, fabric register bank, guarded calibration, and
  pin-facing I²S/model hierarchy. Prove 15 complete 5 MHz frames through the
  actual stack, including startup commit/readback, retained and refreshed
  force-mute snapshots, a snapshotted short-frame fault and transport count,
  and exactly one diagnostic clear in the unrelated BCLK domain. Synthesize the
  flattened hierarchy to
  19,719 LC / 18,856 FF / 216 DSP48E1 / 8 RAMB18E1 + 1 RAMB36E1 with zero
  structural-check problems; placed timing and a physical host backend remain
  open.
- [x] Implement an oversampled SPI mode-0 transport for the fabric register bus
  without a derived clock. Prove eight 80-bit transactions through the real
  register/calibration guard at 5 MHz, including identity read, calibration
  writes/commit/readback, bus-error status, short frame, withheld response,
  diagnostic clear, and saturating completion count. Synthesize warning-free to
  112 LC / 172 FF / no DSP or RAM. The complete composition is recorded above.
- [x] Integrate the fabric register bank around the pin-facing mono hierarchy.
  Freeze 20 fabric-coherent diagnostic words, synchronize four sticky I²S
  faults, transfer diagnostic clear by one toggle event, and own calibration/
  mute through the bus. Prove retained snapshots, startup calibration, and one
  I²S clear pulse across unrelated clocks; synthesize the crossing to 1 LC /
  5 FF and the complete wrapper to 19,616 LC / 18,684 FF / 216 DSP48E1 /
  8 RAMB18E1 + 1 RAMB36E1. No Fmax is claimed.
- [x] Implement a protocol-neutral fabric control register bank with reset-muted
  state, a coherent calibration shadow/commit transaction, distinct attempted
  and accepted sequences, retained rejection/bus errors, pulsed diagnostics
  clear, and atomic diagnostic snapshots. Prove accepted, invalid, unsafe,
  busy-write, bad-address, and snapshot-retention behavior warning-free;
  synthesize to 323 LC / 715 FF / no DSP or RAM. Pin and SPI integration are
  recorded above.
- [x] Test three schedule-neutral refinements to the remaining trapezoidal
  terminal error. Preserve exact negative results showing that within-sample
  bank reselection worsens 1.5 V/recovery, 5/4 residual relaxation improves
  burst error but displaces recovery state, and full dual-triode/stage-one-
  split Jacobian banks either fail cross-level validation or create 58
  residual-limit misses. Retain the production coefficients and schedule.

- [x] Implement and integrate a Gray-counter BCLK/fabric rate monitor. Require
  three consecutive 1,024 ± 1 edge windows for lock, drop lock and latch a bad
  window, reacquire after correction, clear retained evidence, detect a stopped
  BCLK as zero edges, and revoke live state on BCLK reset. The actual-rate pin
  test measures 1,024 edges across four
  windows without changing audio/latency. Synthesize standalone to 68 LC / 125
  FF and the updated pin top to 19,156 LC / 17,669 FF / 216 DSP48E1 /
  8 RAMB18E1 + 1 RAMB36E1.
- [x] Add conservative local-domain occupancy and retained high-water
  diagnostics to both sides of each asynchronous FIFO. Reach exact depth eight,
  drain to zero, clear watermarks, and preserve the 128-word wrap test. At the
  bridge, backpressure records RX 3/3 and TX 4/4 frames without loss; at the
  locked pin-level rate all four views peak at one frame without changing audio
  or latency. Updated synthesis is FIFO 127 LC / 331 FF, bridge 571 LC / 1,547
  FF, and the later clock-monitored pin top 19,156 LC / 17,669 FF; no DSP/RAM
  change from diagnostics.
- [x] Correct the pin-level integration clocks from the accidentally ratio-only
  100/3.125 MHz test to the stated 98.304/3.072 MHz rates. Timestamp internal
  handshakes and serial boundaries; gate the deterministic intervals and record
  192 BCLK / 62.500 us / 3.000 sample periods from the first complete ADC frame
  to the first complete valid model-output DAC frame. Keep this transport result
  separate from resampler/circuit and physical-converter group delay.
- [x] Compose the I²S/CDC bridge with the calibrated accuracy-first mono
  adapter. Under exactly frequency-locked 3.072/98.304 MHz clocks with unrelated
  phase, deliver all 64 serial stereo inputs to calibrated model state exactly,
  match all raw model outputs, and recover 45 consecutive observable DAC frames
  as exact mono duplicates. Retain expected startup starvation and zero all
  other diagnostics; atomically commit the startup converter-scaling pair while
  muted and reject a later live pair without changing active values; synthesize
  the later clock-monitored top to 19,156 LC / 17,669 FF /
  216 DSP48E1 /
  8 RAMB18E1 + 1 RAMB36E1 with no placed CDC/I/O/converter claim.
- [x] Add a protocol-neutral atomic calibration commit guard. Reset both active
  Q8.24 coefficients inactive, accept a positive pair only while fully muted,
  acknowledge the pair together, and preserve active values on invalid or live
  attempts with separate sticky diagnostics. Pass warning-free directed and
  pin-top regressions; synthesize the standalone guard to 14 LC / 67 FF / no
  DSP or RAM.
- [x] Compose the framed mono fabric datapath from scheduler through input
  calibration, exact trapezoidal/banked/terminal stream, output calibration,
  held ready/valid output, and explicit mono duplication. Match 64 calibrated
  inputs, raw model outputs, and PCM frames bit-for-bit under five clocks of
  output backpressure; force and clear one output overrun without overwriting
  the held frame while model/calibration diagnostics remain zero. Prevent the discovered hidden
  startup-state advance by holding the core reset through phase acquisition;
  integrate the downstream safety ramp and synthesize the combined hierarchy to
  18,642 LC / 16,354 FF / 216 DSP48E1 /
  8 RAMB18E1 + 1 RAMB36E1 with no structural problems and no timing claim.
- [x] Correct synthesis resource accounting to retain both RAMB18E1 and
  RAMB36E1 primitives plus their 18-Kib equivalent total. Existing factorized
  hierarchies use 8 RAMB18E1 + 1 RAMB36E1, not the formerly reported eight
  RAMB18E1-only count; numerical implementation is unchanged.
- [x] Align asynchronous-bridge frames to the solver's deterministic fabric
  schedule. Accept one held stereo frame per 2,048-clock period, prelaunch for
  one-clock calibration, inject zero on starvation, and retain a saturating
  underflow count. Verify phase zero and directed A/zero/B order warning-free;
  synthesize to 41 LC / 43 FF / no DSP or RAM.
- [x] Define and implement the converter calibration boundary without selecting
  hidden gain: PCM24 to input-referred Q8.24 volts and physical Q8.24 line volts
  to saturating PCM24. Match 4,159 Python/RTL vectors per direction with
  explicit endpoint, saturation, and invalid-coefficient diagnostics; synthesize
  to 95/86 LC, 66/58 FF, and 4 DSP48E1 per direction with no warnings.
- [x] Integrate the I²S protocol and CDC primitives into a bidirectional stereo
  frame bridge. Preserve 20 exact BCLK-to-fabric-to-BCLK frames under unrelated
  clocks and deliberate ready backpressure, verify owning-domain diagnostics,
  and synthesize the later instrumented hierarchy to 571 LC / 1,547 FF with zero
  structural problems and explicit register-expanded FIFO storage.
- [x] Implement conventional 24-bit stereo I²S in 32-BCLK slots. Loop 16 signed
  frames exactly through warning-free receive/transmit RTL; independently check
  32-period slots and delay bits; inject framing and underflow faults; synthesize
  RX/TX to 35/97 LC and 105/137 FF with no warnings or structural problems.
- [x] Implement a device-neutral dual-clock FIFO with Gray pointer crossings,
  two-flop synchronizers, registered read data, sticky overflow/underflow, and
  embedded formal invariants. Preserve directed and 128 wrapped words under
  unrelated clocks; with later occupancy watermarks, synthesize depth 8×32 to
  127 LC / 331 FF with zero
  structural problems and a documented register-expansion warning.
- [x] Add nine original, physically scaled PCM24 regressions covering silence,
  nominal/low-level THD, high-frequency intermodulation products, multitone,
  warp, pop, log sweep, and 1.5 V overload. Process 32,448 outputs / 519,168
  nonlinear updates with zero model diagnostics or WAV clips; measure
  0.019826%/0.011559% H2--H10 THD at 5/0.5 mV peak.
- [x] Extend the deterministic audio suite to 14 vectors / 69,440 external
  frames / 1,111,040 nonlinear updates. Add a 60 Hz/7 kHz, 4:1
  SMPTE-RP-120-style sideband profile (explicitly not an analyzer-conformance
  claim), a differential 5 mV one-sample impulse, and paired 250 ms nominal/
  0.5 V overload trajectories. With zero fixed diagnostics or WAV clips,
  measure 0.461295% profile IMD, a strictly causal 34-sample impulse onset and
  138.118 mV peak, and 147.750 ms 10%-nominal recovery relative to the input
  burst stop.
- [x] Add dependency-free 16/24/32-bit PCM WAV I/O, explicit peak-voltage
  scaling through the exact fixed V1 stream, and transparent latency/gain/
  fractional-delay null tooling. Run a 1,024-frame terminal-trapezoidal audio
  regression with zero diagnostics/clips, exact recovery of an injected
  23-sample delay, and separate +2.405/-30.462/-100.810 dB raw/latency/gain
  residuals.
- [x] Capture the complete trapezoidal terminal stream at 100 Hz, 1 kHz,
  10 kHz, and 20 kHz for 4,800 outputs each. Prove fixed/RTL identity and zero
  diagnostics; bound gain/phase error to 0.000134 dB / 0.000444 degree; and
  separate the 87.89 uV worst fitted startup drift from the -74.79 dB
  detrended waveform null.
- [x] Implement trapezoidal terminal correction with exact corrected Q4.44
  capacitor-current commit on the final chord edge. Match all state across
  384,000 overload updates with zero diagnostics; reduce 1.0/1.5 V burst RMS
  error to 4.709/3.604 mV; carry it through 64 complete-stream outputs; and
  synthesize the then-current 127-clock solver/stream to 14,945/20,241 LC,
  174/222 DSP48E1, and 8 RAMB18E1 + 1 RAMB36E1. Later controlled builds are
  recorded separately rather than rewriting this historical milestone.
- [x] Separate all 16 internal frequencies that fold to ±3 kHz in the captured
  complete-stream stress test. Prove the isolated 45 kHz third-harmonic output
  is exactly zero in Q8.24, capture the combined out-of-band projection exactly,
  and measure only a -176.96 dBc complete-vs-family-removed effect below fixed
  rounding closure; the nonfolded 3 kHz bin dominates by 102.37 dB.
- [x] Capture the banked terminal RTL through 384,000 control/overload updates
  at 20 mV, 0.5 V, 1.0 V, and 1.5 V. Preserve H1--H10, clipping asymmetry,
  grid current, recovery, and null metrics; prove full-state fixed equivalence
  and zero diagnostics while matching analytical burst THD within 0.00122
  percentage points and phase within 0.00221 degrees.
- [x] Carry the banked terminal solver through the complete mono resampling
  stream. Match 64 external outputs / 1,024 nonlinear updates exactly at the
  measured 127-clock solver latency with zero diagnostics, and synthesize the
  full hierarchy to 18,466 LC / 168 DSP48E1 / 8 RAMB18E1 + 1 RAMB36E1.
- [x] Implement the backward-Euler terminal correction in fixed Python and
  synthesizable RTL. Prove output/state identity to conventional four-pass,
  match 18,432 overload updates exactly at 127 clocks with zero diagnostics,
  and synthesize to 13,296 LC / 120 DSP48E1 / 8 RAMB18E1 + 1 RAMB36E1.
- [x] Sweep three through six corrections on the current banked solver for both
  integrators at 1.0/1.5 V over 100 ms. Measure fourth-pass burst improvement
  of 5.65--9.02 dB, six-pass residual <=0.207 uA, non-monotonic recovery-state
  error, and the rejected 145-clock minimum extra-pass projection.
- [x] Split integer tube evaluation from fixed circuit/state/chord error using
  the same Q24/Q20 input and Q31 current interfaces. Prove all intermediate
  banked runs diagnostic-clean; measure <=0.168 mV tube-evaluator burst error
  versus 6.40--19.07 mV circuit/state/chord error.
- [x] Decompose banked severe-overload error, sweep the grid-current table, and
  implement the selected 1,024-entry branch in fixed Python and RTL. Reduce
  direct worst error from 716 to 12.55 nA and 1.5 V final error from
  18.27/17.36 mV to 0.631/0.321 mV, preserve zero diagnostics, prove standalone
  and 36,864-state integrated RTL exactness, and retain eight mapped RAMB18E1s plus one RAMB36E1.
- [x] Add a Vgk-slew-qualified shallow bank for the severe cutoff arc. Preserve
  bit-exact <=1.0 V behavior, remove all 1.5 V residual-limit misses in both
  integration modes, prove 36,864 RTL states exact with every bank exercised,
  and retain the 116-clock schedule with no added DSP or block RAM.
- [x] Separate the factorized plate-law domain from its grid-current lookup.
  Prove every former 1.5 V range event was only `Vgk < -5 V`, expand plate-law
  acceptance to -8 V while retaining the -5 V grid leakage-floor clamp, and
  prove before/after audio bit-exactness. Exact integrated RTL now has zero
  arithmetic/range/fallback events at 1.5 V; the later slew-qualified bank
  closes the then-remaining 57/53 residual misses.
- [x] Tighten the shallow trapezoidal bank threshold from -2.50 to -2.75 V.
  Avoid every 0.5 V activation, retain zero 1.0 V failures and exact RTL, and
  reduce the final-window mean error from 1.042 to 0.537 mV.
- [x] Compare 100 ms banked waveforms against full Newton without alignment.
  At 1.0 V, improve raw burst error from -53.45/-53.65 dB to -76.43/-76.79 dB
  for backward Euler/trapezoidal; retain the trapezoidal 0.537 mV final-window
  mean error as an open selector/state discrepancy.
- [x] Implement integration-mode-specific cutoff-Jacobian banks in RTL; prove
  all 9,216 overload states per mode bit-exact, exercise every bank at the
  unchanged 116-clock latency, and synthesize without added DSP or block RAM.
- [x] Derive fixed cutoff-region Jacobian banks from the analytical stage-two
  trajectory. In the 100 ms Python gate, remove all 1.0 V residual failures in
  both integration modes without extra corrections, arithmetic/range events,
  or fallbacks; retain the separate 1.5 V residual limitation explicitly.
- [x] Prove wide RHS, backward-Euler/trapezoidal KCL, tube-stamp, and chord
  arithmetic bounds with conservative full-interface integer intervals. All 47
  checks pass; directed regressions cover the corrected 44-bit capacitor delta,
  34-bit `INT32_MIN` cathode-current sum, and saturating tube-pin conversion.
- [x] Establish repository engineering instructions and reproducible tool bootstrap.
- [x] Capture wide-solver RTL at 100 Hz, 1 kHz, 10 kHz, and 20 kHz; prove Q32
  fixed equivalence and <=0.0001943 dB / <=0.0009814 degree analytical error.
- [x] Capture 100 ms overload/recovery trajectories through 1.5 V; compare all
  state exactly and extend post-burst observation to 85 ms.
- [x] Capture the 16× decimator's cubic nonlinear alias trajectory; match 8,192
  outputs exactly and measure -137.814 dBc with zero saturation.
- [x] Integrate frame-aligned reset/warmup and the mute ramp around the wide
  stream; prove no state-reset sample escapes and synthesize the guarded top.
- [x] Compare 768 kHz backward Euler with SPICE at 100 Hz, 1 kHz, 10 kHz, and
  20 kHz; expose 4.72 degree high-frequency phase error and measure a floating
  trapezoidal candidate at <=0.0582 degrees for 10/20 kHz.
- [x] Compare 100 ms backward-Euler/trapezoidal overload trajectories through
  1.5 V; prove finite convergence and matched clean-region recovery.
- [x] Implement explicit fixed trapezoidal capacitor branches with Q30 voltage
  and signed Q4.44 previous-current history; pass the six-frequency nominal
  sweep with zero diagnostics.
- [x] Run fixed trapezoidal overload through 1.5 V; pass the <=0.5 V clean
  region, bound stored capacitor current, and expose the required 48-bit
  companion-conductance width.
- [x] Widen the KCL capacitor coefficient to signed 48-bit, add explicit
  previous/current-next ports, and pass 1,024 exact trapezoidal vectors without
  regressing the backward-Euler KCL.
- [x] Add persistent Q4.44 current state and a separate trapezoidal chord-
  inverse ROM to the selectable solver; match all 29 state words and diagnostics
  across 512 samples at 116 clocks and synthesize the hierarchy.
- [x] Carry trapezoidal state through the complete interpolator/solver/
  decimator stream; match 64 outputs / 1,024 internal updates with zero
  diagnostics and synthesize the selectable hierarchy.
- [x] Capture trapezoidal solver RTL at 100 Hz, 1 kHz, 10 kHz, and 20 kHz;
  prove complete fixed-state equivalence, nominal diagnostics, and bounded
  gain/phase error while linking the separate ngspice integration layer.
- [x] Capture the complete 48 kHz trapezoidal stream for 4,800 outputs at each
  of 100 Hz, 1 kHz, 10 kHz, and 20 kHz; prove exact fixed equivalence, zero
  diagnostics, and <=0.000111 dB / <=0.001185 degree error against the composed
  floating model. Measure the rate converters independently at exactly 51
  external samples / 1.0625 ms so their phase is not attributed to the circuit.
- [x] Extend floating trapezoidal overload observation to 235 ms after the
  burst. Measure 0.5 V 10%-nominal recovery at 146.552 ms, fit the coupled
  stage-two recovery modes at 98.2--118.1 ms, retain 1.0/1.5 V crossings as
  labeled projections, and record complete node/capacitor checkpoints.
- [x] Directly simulate nominal, 1.0 V, and 1.5 V floating trajectories through
  850 ms. Falsify the earlier single-exponential projection, measure 1.0 V
  sustained 10% recovery at 270.112 ms, and expose 413--451× late rebounds
  after opposing circuit modes temporarily cancel near 316--362 ms.
- [x] Capture selectable trapezoidal RTL through the accepted 0.5 V overload
  and 235 ms recovery window. Match 384,000 complete fixed-state updates with
  zero diagnostics and measure sustained 10% recovery at 146.570 ms, 18.23 µs
  from the independent floating trajectory.
- [x] Linearize the actual nine-node/tube circuit at DC and solve `det(G+sC)=0`
  without a generalized-eigenvalue dependency. Verify eight stable finite modes;
  identify 143.936 ms and 1.067763 s output-coupling modes that explain the
  overload cancellation/rebound and bound the next direct record at seven seconds.
- [x] Run seven-second nominal/1.0 V/1.5 V recovery trajectories. Measure all
  sustained 10%/1%/1 mV crossings through 6.371 s; validate the late two-pass
  chord handoff against Newton below 33.2 nV over 100 ms and 17.9 nV at the
  final-cycle probe, with zero solve failures.
- [x] Select, document, and version the Kennedy 1998 two-stage passive-RIAA circuit.
- [x] Implement AT-VM95E R/L/47.5 kΩ/150 pF cartridge loading.
- [x] Build ngspice DC, 10 Hz–100 kHz AC, transient, and 1 kHz H1–H10 level sweeps.
- [x] Verify nominal DC and quantify historical RIAA error without correcting it.
- [x] Implement canonical mathematical RIAA and regress against Bulletin E1.
- [x] Implement the Koren 12AX7 analytical/grid-current model and compare checked
  manufacturer-curve digitization.
- [x] Implement the 768 kHz nonlinear nodal/capacitor-state Python model and
  compare it with ngspice.
- [x] Characterize one through four Newton passes at 20 mV peak.
- [x] Reject raw linear-network fixed-point iteration and select three-pass
  quiescent-Jacobian chord iteration as the measured fixed/RTL candidate.
- [x] Implement reproducible 12AX7 tube LUTs, study four resolutions, and record
  mean/worst interpolation error.
- [x] Define tube-interface Q formats and a bit-accurate Python LUT model.
- [x] Define all V1 state/matrix/residual/inverse formats and implement an
  integer-only three-pass chord model with explicit rounding and saturation.
- [x] Decompose initial multitone error into tube-LUT and fixed-state/chord layers.
- [x] Design the four-stage 16× float/Q1.23-coefficient half-band reference,
  measure response/latency, and verify rejection of a nonlinear 45 kHz alias.
- [x] Implement the fixed Q8.24/Q1.23 per-stage MAC/rounding/saturation model and
  preserve the nonlinear alias test as a regression.
- [x] Reduce chord correction to DSP-native 18×25 operands; measure its error
  independently against the original Q17.15 × Q4.44 correction.
- [x] Implement, lint, synthesize, and verify the nine-node chord-correction RTL
  against 1,024 exact vectors including saturation boundaries.
- [x] Add CI jobs for Python/RTL/generated-asset regressions and ngspice/model
  cross-comparisons.
- [x] Implement synthesizable eight-clock 12AX7 RTL with range diagnostics.
- [x] Pass warning-free Verilator lint and 4,096 bit-exact randomized vectors.
- [x] Run generic XC7 synthesis and record actual structural resource use.
- [x] Implement exact capacitor-history RHS and heterogeneous-format KCL RTL;
  pass 1,024 vectors per block including residual saturation boundaries.
- [x] Integrate both 12AX7 halves, all ten capacitor branches, three corrections,
  final residual, state commit, and runtime diagnostics in a mono scheduler.
- [x] Match all nodes, capacitor states, output, residual, and counters for 512
  sequential fixed-model/RTL samples at a measured 126-clock latency.
- [x] Synthesize the complete hierarchy: 8,024 estimated XC7 logic cells,
  89 DSP48E1s, and 47 RAMB18E1s, with no structural check problems.
- [x] Implement serial-MAC half-band interpolator/decimator primitives and the
  complete 48↔768 kHz four-stage chains with saturation/overrun diagnostics.
- [x] Match 2,048 interpolation and 128 decimation stream outputs exactly;
  record the visible 18-internal-sample scheduler delay and structural resources.
- [x] Integrate the complete 48 kHz reference stream around the nonlinear solver,
  including saturating Q12.20-to-Q8.24 output conversion and diagnostics.
- [x] Match 64 consecutive end-to-end outputs / 1,024 nonlinear updates exactly;
  synthesize the full stream at 13,170 estimated LC, 137 DSP, and 47 RAMB18.
- [x] Sweep analytical and fixed behavior from 0.5 mV to 5 V at 1 kHz using the
  settled SPICE analysis window; quantify THD, compression, residual, and clips.
- [x] Measure low-level distortion at four larger LUT resolutions and reject a
  raw BRAM increase as an ineffective fix.
- [x] Implement and measure a fixed factorized Koren candidate using three
  value/slope 1-D LUTs with cubic Hermite interpolation: 51.8 nA worst current
  error and 0.0188% versus 0.0191% analytical THD at 5 mV.
- [x] Implement the standalone factorized tube RTL and pass 4,110 bit-exact
  randomized/boundary vectors at eight clocks, including five clip cases;
  after the grid-resolution implementation, synthesize at 1,496 LC,
  35 DSP48E1, and 8 RAMB18E1 + 1 RAMB36E1.
- [x] Integrate the factorized primitive as a selectable solver mode; match all
  state and diagnostics for 512 samples at 126 clocks and synthesize the full
  hierarchy at 9,148 LC, 108 DSP48E1, and 8 RAMB18E1 + 1 RAMB36E1.
- [x] Propagate factorized mode through the complete stream; match 64 outputs /
  1,024 circuit updates exactly with zero diagnostics and synthesize at 14,290
  LC, 156 DSP48E1, and 8 RAMB18E1 + 1 RAMB36E1.
- [x] Sweep 5 mV factorized fixed vs analytical at 20/50/100 Hz and
  1/10/20 kHz: ≤0.00846 dB gain error, ≤0.0729° phase error, and no diagnostic
  failures across 683,520 nonlinear samples.
- [x] Characterize 5 ms overload bursts at 20 mV, 0.5 V, 1.0 V, and 1.5 V,
  including peak grid current, clipping asymmetry, residual/range diagnostics,
  and recovery relative to an undisturbed nominal trajectory.
- [x] Sweep three through six chord corrections at 1.0/1.5 V; quantify residual,
  output error, range events, and the 126-to-213-clock serialized projection.
- [x] Run a 768,000-sample silence/bipolar-click state audit with node and all
  capacitor checkpoints; expose the Q12.20 deadband and preserve it as a
  reproducible regression rather than hiding it with output DC removal.
- [x] Implement a 40-bit Q28/Q32 node, Q30 history, branch-current Python
  candidate with staged Q30/Q34/Q40 correction precision. Reduce the click
  audit's late residual from 5.375 mV to 38.74 uV and the nominal 1 kHz raw null
  from -42.90 to -63.83 dB with zero diagnostics.
- [x] Sweep the wide-state candidate at 20/50/100 Hz and 1/10/20 kHz: bound
  gain/phase error to 0.000196 dB / 0.000982 degrees with zero diagnostics.
- [x] Re-run 20 mV--1.5 V overload with adaptive Q30/Q34/Q40 residual scaling:
  eliminate arithmetic saturation and improve clean-region recovery/error, but
  retain explicit 1.0/1.5 V convergence and 1.5 V range failures.
- [x] Implement the 40-bit Q28/Q32 chord corrector with bounded Q30/Q34/Q40
  scaling; match 1,024 vectors at ten clocks and synthesize to 1,701 XC7 logic
  cells / 9 DSP48E1 / no RAMB18. Reject the 5,531-cell arbitrary-shift version.
- [x] Implement two-clock wide RHS and ten-clock branch-current KCL blocks;
  match 1,024 vectors each with adaptive fallback, true overflow, and delayed
  tube-current coverage. Synthesize at 31 LC / 4 DSP and 8,034 LC / 72 DSP.
- [x] Integrate the wide factorized solver; match all 19 persistent states and
  diagnostics across 512 sequential samples at 116 clocks. Synthesize the
  hierarchy at 12,544 LC / 120 DSP48E1 / 8 RAMB18E1 + 1 RAMB36E1.
- [x] Integrate the wide solver into 16x interpolation/decimation; match 64
  outputs / 1,024 solves exactly with zero diagnostics and synthesize at 17,492
  LC / 168 DSP48E1 / 8 RAMB18E1 + 1 RAMB36E1.
- [x] Capture 23,040 wide-solver RTL samples at 5 mV/1 kHz; prove Q32 exactness
  and measure -0.000054 dB gain, -0.000187 degree phase, 0.019371% THD, and
  -63.834 dB raw residual directly from RTL output.
- [x] Implement and test a downstream Q0.16 output mute/ramp with reset-muted
  startup, symmetric rounding, exact-unity bypass, and synchronous fault clamp;
  synthesize at 171 XC7 logic cells, 2 DSP48E1s, and no block RAM.
- [x] Quantify flat/partial/full-analog RIAA front-end architectures.
- [x] Produce initial gain/headroom, MM loading, noise, converter, clock, control,
  safety, stereo schedule, and hardware-verification engineering documents.

## Known discrepancies and failing regressions

- No failing regression.
- Python backward-Euler MNA versus ngspice ranges from -66.42 dB raw residual at
  100 Hz to -21.50 dB at 20 kHz. The 20 kHz gain error is only -0.0646 dB, but
  phase error is +4.72 degrees. Floating trapezoidal reduces that phase error to
  +0.0582 degrees. The fixed trapezoidal model is now nominally bounded against
  that floating candidate and implemented through the complete RTL stream. The
  legacy unbanked solver still fails severe-overload convergence; the selected
  banked terminal path is diagnostic-clean through the tested 1.5 V burst but
  retains 3.604 mV trapezoidal burst RMS approximation error. The SPICE link is
  still based on separate, non-sample-identical transient stimuli.
- The frozen historical circuit is -0.919 dB from ideal RIAA at its worst audio-
  band point. This is reference behavior, not an implementation defect.
- The explicit 2-D-LUT RTL mode produces 0.0733% THD versus 0.0191% analytical
  at 5 mV/1 kHz. The separately selectable, fully integrated factorized RTL mode
  reduces this to 0.0188%; both modes remain named and independently verified.
- At 1.0 V peak the factorized fixed candidate records 5,209 residual-limit
  failures and 7.03 µA maximum residual; overload solver behavior remains open.
- In a 5 ms burst, factorized residual-limit failures begin at the tested 1.0 V
  level (1,134 samples); 1.5 V causes 4,046 transformed-domain clip events.
  Bursts ≥0.5 V do not recover below 10% nominal RMS within the 35 ms window.
- The Q12.20 output/capacitor state can freeze after a discontinuity. In the
  one-second bipolar-click audit the final fixed output is -5.368 mV versus
  4.5 uV instantaneous analytical output; no runtime diagnostic fires.
- The wide candidate fixes that state deadband but not severe nonlinear
  convergence: 1.0/1.5 V bursts still exceed the residual limit 1,122/1,695
  times, and the latter clips the transformed tube domain 4,046 times.
- Yosys reports 204 Xilinx BRAM primitive port-resize warnings on the hierarchical
  solver while `check` reports no structural problem. Track tool-version behavior;
  do not describe synthesis as warning-free.

## Research and hardware questions

- Obtain better positive-grid 12AX7 data and quantify grid-current/overload error.
- Evaluate piecewise/hybrid tube approximation if full circuit synthesis proves
  the 47-RAMB18 primitive to be the dominant capacity constraint.
- Fabricate and measure the routed OPA1656/PCM4202 Architecture A EVT board,
  then compare at least one alternate ADC/front end before freezing production
  converter, gain, or anti-alias parts.
- Determine a credible stereo architecture; the selected solver uses 127/128
  clocks and cannot be time-multiplexed across two channels at the present
  throughput. The calibrated, muted pin-facing mono hierarchy uses 232/240 A7-100T
  DSPs, preventing duplication.
- Select a first full integrated-amplifier topology only after V1 phono equivalence.

## Verification debt

- The full-phono circuit RTL is bit-exact to fixed Python and now has nominal
  four-point solver and complete-stream captures. SPICE comparison remains at
  four frequencies and large-signal cross-layer coverage is still incomplete.
- PCM WAV processing, explicit null comparison, and deterministic distortion,
  IMD-product, SMPTE-profile, impulse, and paired long-recovery gates now exist.
  The SMPTE-profile sideband fit is traceable but is not a calibrated RP 120
  instrument implementation; licensed/user-supplied music remains absent. The
  I²S protocol and CDC FIFO primitives now form a bidirectional frame bridge, and standalone
  physical-unit calibration now composes with the accuracy-first mono core at
  the fabric frame boundary and a pin-facing top adds the asynchronous bridge.
  The modeled-output ramp and atomic converter-coefficient commit are now
  integrated, and the SPI-controlled pin wrapper supplies transport, shadow
  commit, and coherent fabric snapshots. A tested host codec/client now defines
  framing and guarded operations; a physical adapter backend,
  queued-frame/physical analog muting, and CDC/I/O timing constraints remain
  absent. The single-clock mute/ramp properties now have a Yosys SAT proof;
  asynchronous-FIFO properties now have a 32-step arbitrary-clock SAT bound,
  while a complete invariant set for unbounded induction remains open.
  The cubic and full-tube alias-family tests are captured from RTL; the latter
  is bounded below fixed rounding closure rather than inferred from the
  confounded raw bin.
- No qualified named-speed-grade Fmax, FPGA capture, analog converter, or physical tube
  measurement exists.
- GE curve digitization has ±0.05 mA visual uncertainty; production tube spread
  and tolerance statistics are not characterized.
- Front-end noise excludes flicker, hum, EMI, protection parasitics, distortion,
  reference noise, and PCB effects until physical measurement.

## Later milestones

- [ ] Stereo scheduling and converter interface on Arty A7-100T reference platform.
- [x] Standalone 24-bit/32-slot I²S receive/transmit protocol primitives.
- [x] Bidirectional stereo-frame I²S/fabric asynchronous bridge.
- [x] Bit-exact PCM24/input-volts/output-volts calibration primitives.
- [x] Frequency-locked bridge-to-core fabric frame scheduler.
- [x] Calibrated framed mono adapter around the accuracy-first V1 stream.
- [x] Pin-facing digital I²S/CDC plus calibrated mono-model integration.
- [x] Atomic muted converter-calibration commit boundary and diagnostics.
- [x] PCM WAV processing and latency/gain/fractional-delay null comparison.
- [x] Deterministic WAV distortion/IMD-product/overload regression library.
- [x] Traceable SMPTE-profile sideband, paired long-recovery, and impulse WAV
  gates.
- [ ] Licensed/user-supplied music WAV gate with provenance and redistribution
  rights.
- [ ] Fabricated MM front end, ADC/FPGA/DAC loopback, and calibrated line output.
- [ ] Validated phase inverter, power tubes, transformer, dynamic supply, feedback,
  and speaker interaction for one selected integrated-amplifier circuit.
- [ ] Transparent protected physical power stage; FPGA/DAC never drive speakers directly.
