birdybro/FPGA_Amp/docs/adc_dac.md

# ADC, DAC, and audio clocks

No converter is released for a production PCB. PCM4202 and PCM5242 are selected
for the routed Rev-A input and output EVT boards so their clock, driver,
headroom, mute, and layout assumptions can be tested. The following official
specifications narrow prototype work; they are not claims about measured
performance.

## ADC candidates

| Candidate | Relevant published capability | Engineering position |
|---|---|---|
| AKM AK5572EN | 2-channel differential, up to 768 kHz, 121 dB dynamic range, 112 dB S/(N+D), 124 dB mono mode, TDM | Leading high-performance prototype candidate; confirm exact full scale, group delay, supply/reference, and current availability in data sheet |
| TI PCM4202 | 2-channel, 24-bit, 216 kHz, 118 dB A-weighted / 116 dB unweighted typical dynamic range at 48 kHz, -105 dB THD+N, I²S | Selected for the unbuilt Rev-A EVT board; validate performance, availability, and 128-fS serial timing before production selection |
| TI TAA5242 | 2-channel, 192 kHz, 119 dB dynamic range, 2 V RMS differential full scale, I²S/TDM | Convenient match to the quantitative 2 V/119 dB front-end study; -98 dB THD+N may limit high-level transparency |

The initial board should expose converter clipping before any digital scaling.
At 48 kHz operation, a 24.576 MHz master allows standard clock ratios, but the
analog anti-alias path must suppress energy above Nyquist. Running the ADC at
96/192 kHz and explicitly decimating before the 48 kHz model is an alternative
if measured RF/alias performance justifies the added block and latency.

## DAC candidates

| Candidate | Relevant published capability | Engineering position |
|---|---|---|
| TI PCM5242 | 32-bit/384 kHz voltage output, 114 dB SNR, 4.2 V RMS differential, integrated PLL/filters and soft mute | Practical first line-output path with enough voltage headroom; verify residual DSP bypass and latency |
| TI PCM1792A | 24-bit/192 kHz current output, 127 dB stereo dynamic range, -108 dB THD+N | Higher performance ceiling, but external I/V and mute circuitry add analog noise and complexity |
| AKM AK4493S | 32-bit/768 kHz, 123 dB S/N and -115 dB THD+N at 2 V RMS published | Strong performance candidate; supply, filter, clock, availability, and output-stage implementation still require detailed review |

Reference line output needs about 2.25 V RMS at a 20 mV RMS 1 kHz cartridge
input. A 2 V RMS DAC therefore needs calibrated attenuation or a post-DAC gain
stage; the 4.2 V RMS differential PCM5242 class offers more direct headroom.
Reconstruction filtering and line-driver load are measured as part of the full
path, never subtracted from a data-sheet number.

### Rev-A PCM5242 output contract

The routed `hardware/kicad/dac_line_output_eval_rev_a/` board makes the first
selection concrete without promoting it to production status. PCM5242 runs as
a 48 kHz slave with 24-bit I2S in 32-BCK channel slots, external 24.576 MHz SCK,
3.072 MHz BCK, I2C mode, and its ground-centered VREF output setting. Reference
firmware must configure and read back a unity path while XSMT remains low; the
integrated miniDSP is not part of historical/reference processing.

The balanced branch follows the official EVM's 499 ohm per-leg / 1 nF
differential reconstruction network. Into 20 kilohm it calculates to 4.00038 V
RMS at DC and 3.97214 V RMS at 20 kHz (-0.0615 dB relative). The RCA branch uses
499 ohm / 2.2 nF single-ended filtering and calculates to 2.00019 V RMS at DC
and 1.98314 V RMS at 20 kHz into 10 kilohm (-0.0743 dB). These are circuit
calculations, not measurements.

Three normally-open G6K relays make loss of power a physical open-circuit mute.
Separate SN74LVC1G08 gates require both controller permission and an independent
active-high supervisor release (`HARD_MUTE_N`) before either relay drive or DAC
XSMT can assert. All permission inputs and XSMT have fail-low pull-downs. This
prevents a stuck controller from overriding the external mute supervisor; it
does not replace required sequencing and transient measurements.

The four-layer 112 x 72 mm route has 581 segments and 86 vias. KiCad 10.0.5
reports zero ERC, zero DRC, and zero unconnected items, and the source-aware
verifier locks the converter/interlock/relay maps and calculated loading. It
remains unbuilt pending register readback/status control, loaded audio measurements,
mute/brownout tests, connector and chassis qualification, ESD/RF testing,
stackup review, and DFM.

The first synthesizable PCM5242 bootstrap now writes twenty explicitly audited
register transactions through the shared I2C engine's new one-byte-address
mode. A bus-level target model proves the `0x4c` strap address, exact page and
register data, final bus release, and immediate halt on an injected NACK. The
sequence selects external SCK, 24-bit I2S, direct L/R routing, ROM interpolation
program 1, 0 dB digital/analog gain, VREF output, no de-emphasis, and disables
zero-detect auto mute so converter silence recovery is not inserted into the
reference behavior. Yosys reports 83 estimated XC7 logic cells / 86 flip-flops /
no DSP or BRAM / zero warnings. Its `configuration_written` output is not an
unmute permit: critical-register readback plus clock/power-state validation
remain required before the independent board interlocks can be released.

The corresponding single-register read transport is now implemented separately.
It performs the PCM5242-required indirect one-byte read with a repeated START,
returns one byte, terminates it with a master NACK, and honors target clock
stretching. Directed bus simulation proves the exact `0x98`, register, and
`0x99` transmitted bytes, returned data, STOP/release behavior, and an
address-NACK abort. Its generic XC7 structural result is 70 estimated logic
cells / 63 flip-flops / no DSP or BRAM / zero warnings.

The completed startup verifier builds on that transport with 24 exact
operations. It selects page 0, compares normal-operation/mute, PLL, I2S,
routing, DSP program, digital-volume, and auto-mute fields; selects page 1 and
checks VREF, analog gain/mute, and boost fields; then returns to page 0. Status
acceptance requires detected 48 kHz, 512-fS SCK, 64-fS BCK, all clock-valid
flags, the expected unlocked indication for the deliberately disabled PLL, DSP
boot complete, and run state. Reserved bits are excluded by explicit masks.
Any NACK or masked mismatch latches an error with failing index, observation,
expectation, and mask. The directed bus test covers the complete success path,
a program-select mismatch, and a page-1 NACK. Yosys reports 170 estimated XC7
logic cells / 173 flip-flops / no DSP or BRAM / zero warnings. The result is a
startup snapshot, not continuous fault surveillance; the integrated controller
therefore follows it with a separate persistent monitor and still relies on the
external hardware supervisor.

`pcm5242_dac_startup_controller` now performs the complete ordering. It holds a
single fail-low `unmute_permitted` false through the startup delay, 20-write ACK
phase, 24-operation verification phase, and first four-register runtime poll.
The monitor then polls page-0 clock-valid (`0x5e`), latched/live clock-error
(`0x5f`), active/sticky output-short (`0x6d`), and DSP boot/power (`0x76`)
status at a nominal 100 ms interval. Because reads clear the two device-side
sticky histories, the FPGA captures the first failing value and latches fault
until reset. Integration simulation proves 48-transaction release, both startup
failure phases, and post-unmute permission revocation on a short indication.
The monitor alone measures 122 estimated XC7 logic cells / 178 flip-flops; the
complete controller is 340 / 439, with no DSP/BRAM or warnings. Its output is
for the PCB controller-side AND input and does not replace `HARD_MUTE_N`.

## Nominal clock tree

```text
24.576 MHz low-jitter oscillator
  +-> ADC/DAC master clock
  +-> FPGA MMCM -> 98.304 MHz fabric
          +-> ce_sim /128 = 768 kHz
          +-> ce_audio /2048 = 48 kHz
          +-> serial clock scheduling, BCLK = 3.072 MHz for 64-bit stereo frame
```

ADC and DAC share the audio master to avoid asynchronous sample-rate conversion.
The fabric processes a single clock with enables. If a converter or USB source
must become clock master, its serial port crosses through an explicit dual-clock
FIFO and a rate-control policy; two “nominally 48 kHz” oscillators are not
silently connected.

The first timing-closed board candidate uses the Nexys Video's fixed 100 MHz
source and the 384 kHz internal-rate profile instead of the nominal 98.304 MHz
tree above. The implemented XC7-only clock leaf is:

```text
100 MHz board oscillator
  -> MMCM: 12.288 MHz ADAU1761 MCLK
       -> MMCM: 49.152 MHz fabric
            -> ce_sim /128 = 384 kHz
            -> framed scheduler /1024 = 48 kHz
            -> planned BCLK /16 = 3.072 MHz
                 -> shared LRCLK /64 = 48 kHz
```

The exact MMCM ratios are generated and checked by `make audio-clock-plan`;
the clock-only harness is openly synthesized, routed, and converted to a
CRC-readable bitstream. An exact /16 BCLK divider and separate fabric/BCLK
three-edge reset-release synchronizers are now warning-free in RTL simulation
and synthesis. The shared physical LRCLK wrapper and ADAU1761 I2C
configuration are not part of that harness yet.
This is an implementation architecture for the explicit 8x candidate, not a
silent change to 16x reference-mode numerical behavior.

The generic open-drain write engine and codec-specific ordered register table
are now tested and synthesized. The writer supports the ADAU1761's 16-bit
register addresses, checks ACK after all four transmitted bytes, and honors
SCL stretching. Direct 12.288 MHz MCLK selects the 48 kHz family without the
codec PLL; the ADAU1761 remains subordinate to FPGA-provided BCLK/LRCLK. Both
line outputs are set to 0 dB but muted before signal routing, and their unmute
writes are the final two transactions. A NACK aborts the table and preserves
the failed index; the surrounding board top must continue driving zero PCM
unless `configured` is asserted. Register readback is not part of the initial
bootstrap.

The implemented protocol baseline is 24-bit signed I²S in 32-BCLK stereo slots,
so 48 kHz produces the planned 3.072 MHz BCLK. Receiver and transmitter are
separate BCLK-domain primitives with conventional one-bit-delay timing and no
converter-specific register assumptions. A dual-clock FIFO exists for the case
where BCLK/fabric phase is not proven synchronous. A bidirectional bridge now
integrates the protocol blocks with independent depth-8 stereo-frame FIFOs and
held ready/valid fabric interfaces. It deliberately performs no volts/code
calibration, channel scheduling, rate matching between independent nominal
sample clocks, or converter register setup.

### Rev-A phono/ADC clock contract

The routed Rev-A board uses the PCM4202 as the 48 kHz I²S master while the
digital board supplies 24.576 MHz SCKI. Its fixed straps select 512-fS SCKI and
128-fS BCK, producing 6.144 MHz BCK rather than the existing 3.072 MHz/64-fS
RTL baseline. Each half-frame therefore contains 64 BCK periods. The new
receive-only `pcm4202_i2s_capture` captures the 24-bit I²S word after the
conventional one-bit delay, ignores the unused remainder, and crosses complete
stereo frames through a depth-8 asynchronous FIFO into fabric. A 16-frame
6.144/49.152 MHz test with unrelated phase, backpressure, signed endpoints,
held-valid checking, and injected LRCK fault passes. The original 32-BCK mode
also remains regression-tested. Yosys reports 252 estimated XC7 logic cells,
791 flip-flops, no DSP or block RAM, and zero structural problems; its one
warning records register implementation of the small dual-clock memory. This
closes the RTL-format gate, not FPGA-pin timing or physical board validation.
The internal ADC high-pass filter is disabled so reference mode can retain the
modeled circuit's subsonic response.

Separate fabric-domain calibration primitives now implement the exact PCM24 to
physical-Q8.24 boundary. ADC direction uses input-referred peak volts at PCM
full scale; DAC direction uses reciprocal output peak volts and saturates before
serialization. Nonpositive coefficients mute and flag the sample. The
coefficients remain host/measured inputs, so this arithmetic does not select or
validate any listed ADC/DAC and cannot correct historical-circuit response.

The pin-facing top stores the two active coefficients behind an atomic commit
guard. Both reset to zero and accept a positive candidate pair only while the
digital output ramp reports fully muted. Invalid or live attempts preserve the
old pair and set separate sticky diagnostics. This establishes a safe
fabric-domain update boundary; converter register programming and host-to-
fabric CDC remain future board-control responsibilities.

The fabric frame scheduler consumes one held stereo frame at a deterministic
2,048-clock cadence and prelaunches for the one-clock input calibrator. A missing
frame becomes an explicit zero plus underflow count rather than an off-phase
core request. This handles unknown phase only when BCLK and fabric are frequency
locked. A converter with an independent master oscillator still requires an
explicit rate-control/ASRC decision; finite FIFO depth is not rate matching.

The pin-facing digital mono top now composes the bridge, scheduler, calibration,
and selected nonlinear stream. Its regression uses the exact planned ratio,
3.072 MHz BCLK to 98.304 MHz fabric, with independent phase. Bridge fabric reset
is released first; after a received frame crosses and is held, fabric-synchronous
audio reset is released. This proves one reset/rate contract in simulation, not
that either the FPGA or an unselected converter is the hardware clock master.
Each receive/transmit FIFO now reports local-domain occupancy and a retained
high-water mark. At the exact locked test rate all four views peak at one frame.
Write-side values conservatively lag completed reads high and read-side values
lag writes low; polling drift is useful evidence but is neither rate matching
nor a coherent CDC snapshot.

The pin top also instantiates a BCLK/fabric ratio monitor. Its default 333.33 µs
window expects 1,024 ± 1 BCLK rising edges and requires three consecutive good
windows, so nominal lock takes about 1 ms. One bad window drops lock immediately
and latches an error. The exact-rate integration measures 1,024 edges in each of
four windows. The ±1 count tolerance is a coarse ±0.098% configuration check;
smaller sustained differences appear as FIFO occupancy drift. Board startup may
observe this status but must not simply hold the depth-8 receive FIFO undrained
for the entire acquisition interval.

Jitter sensitivity must be checked at the highest analog input frequency. For a
20 kHz full-scale sine, 1 ps RMS aperture jitter alone corresponds to roughly
138 dB SNR; converter internal clocking, oscillator phase noise, and power noise
must be evaluated together rather than quoting one time-domain number.

## Latency accounting

The tube LUT is eight 98.304 MHz clocks (0.0814 µs) per evaluation. Digital
frame flow now exists through I²S, interpolation, solver, decimation, the
modern digital output ramp, and output serialization. The pin-level RTL now
timestamps actual valid/ready and serial-frame events at 3.072 MHz and both
supported fabric rates. From completion of the first ADC PCM frame to completion
of the first corresponding valid model-output DAC frame, both paths measure
exactly 192 BCLKs: 62.500 µs or 3.000 48 kHz sample periods. At
768 kHz / 98.304 MHz, accepted calibrated input to first model output-valid is
277 fabric clocks (2.8178 µs). This is four clocks beyond the older report
because each circular-history 2x decimator performs its center tap in a
dedicated cycle. At 384 kHz / 49.152 MHz the corresponding interval is 265
clocks (5.3914 µs). Mute/output calibration adds two clocks and the held
transmit frame is accepted one clock later in both cases. The detailed reports
are `model/generated/phono_i2s_mono_top_latency.json` and
`model/generated/phono_i2s_mono_top_384khz_latency.json`.

This is transaction/valid transport latency, not signal group delay. The first
fixture code becomes nonzero at output index 19 because of initialized circuit
state, filtering, and PCM quantization; that index is retained as a regression
but is not used as an impulse-delay estimate. The separately measured identity
resampler has 51 samples of causal converter delay, while a real circuit also
has frequency-dependent phase. Converter digital filters, aperture, analog
filters, and board propagation remain unknown. Final end-to-end latency will
use an analog loopback impulse/correlation measurement, not a sum of optimistic
data-sheet typical values.
