birdybro/FPGA_Amp/docs/controls.md

# Control plane and diagnostics

Audio processing accepts a versioned parameter snapshot only on a 48 kHz sample
boundary. Host protocol parsing never writes datapath registers directly. A
shadow bank, commit sequence number, and acknowledge bit make multiregister
changes atomic; model changes invoke mute/state initialization before commit.

The datapath-side reset transaction is implemented by `model_change_guard`.
Software asserts a level request only after `output_ready`, holds it until the
one-cycle acknowledgment, then deasserts it to re-arm the next transaction.
Acknowledgment follows muted core reset plus 64 valid warmup outputs; it does not
claim that ramp-up has reached unity. `change_busy` remains asserted during
ramp-up and `output_ready` identifies the eventual full-gain state. Model-asset
shadow registers and a host protocol remain open.

`phono_control_registers` now supplies the first concrete fabric-domain host
boundary. Its protocol-neutral request/registered-response bus accepts one
32-bit word transaction per fabric clock. It resets with mute asserted, owns a
coherent two-register calibration shadow pair, converts a commit command into
one update pulse, waits for the existing guard response, and records attempted
and accepted transaction sequences separately. Shadow writes are rejected while
a commit is pending. An invalid or live/unmuted attempt advances only the
attempted sequence and latches explicit rejected status; it cannot change the
active pair.

The same block requests one domain-coherent diagnostic capture on a snapshot
command and copies all configured words only when that capture returns valid. A
saturating sequence identifies each completed image, and subsequent reads access
only the retained image. Snapshot busy/available state is observable. The
default 131,072-fabric-clock timeout latches explicit evidence without modifying
the previous image or advancing its sequence. A single control write can also
pulse the existing fabric diagnostic clear and independently clear register-
local sticky evidence.
Verilator proves snapshot retention across changing live inputs, reset-muted
state, accepted/invalid/unsafe calibration transactions, pending-pair write
rejection, busy snapshot rejection, completion, timeout, retained-image
behavior, clear pulses, and bad-address reporting. XC7 structural synthesis is
354 estimated logic cells / 735 flip-flops / no DSP or block RAM; the one Yosys
warning is the expected 16x32 snapshot array expansion to registers. No Fmax is
claimed.

## Implemented word register map

Addresses are word addresses, not byte addresses. There are no partial writes.
SPI, UART, or an embedded processor may translate to this bus without changing
the audio solver.

| Address | Name | Access | Meaning |
|---:|---|---|---|
| `0x00` | identity | R | `0x46504741` (`FPGA`) |
| `0x01` | ABI version | R | major/minor `0x0001_0001` |
| `0x02` | capabilities | R | snapshot, calibration, mute, diagnostic clear |
| `0x03` | live status | R | mute, muted, ramping, commit busy, snapshot valid/busy, capture available |
| `0x04` | control | R/W | bit 0 mute level; bits 1/2/3 snapshot, diagnostic clear, local-sticky clear commands |
| `0x05` | snapshot sequence | R | saturating completed-image sequence |
| `0x06` | calibration attempted | R | saturating commit-attempt sequence |
| `0x07` | calibration accepted | R | sequence of the last accepted attempt |
| `0x08` | ADC calibration shadow | R/W | signed Q8.24 input peak volts |
| `0x09` | DAC calibration shadow | R/W | signed Q8.24 reciprocal output peak volts |
| `0x0a` | calibration command | W | bit 0 commits the complete shadow pair |
| `0x0b` | ADC calibration active | R | guard-owned active coefficient |
| `0x0c` | DAC calibration active | R | guard-owned active coefficient |
| `0x0d` | sticky status | R | bus, rejected, invalid, unsafe, and snapshot-timeout evidence |
| `0x20...` | diagnostic snapshot | R | retained configured diagnostic words |

`phono_i2s_control_top` connects 22 words to that aperture:

| Address | Snapshot contents |
|---:|---|
| `0x20` | clock lock/error, rate-fault mute, scheduled-frame, mute/ramp, calibration/configuration errors, synchronized I²S sticky faults, fabric FIFO faults, SPI frame/response faults, external force mute |
| `0x21` | measurement-valid, lock/error, good-window count, measured BCLK edges |
| `0x22` | fabric RX/TX FIFO level and high-water views plus scheduler phase |
| `0x23` | output gain, solver latency, minimum correction format, mute/ramp |
| `0x24...0x31` | scheduler underflow, input endpoint, output PCM saturation/overrun, resampler saturation/overrun, input phase, output conversion, and six solver counters |
| `0x32...0x33` | 63-bit preterminal solver residual, low word first |
| `0x34` | saturating completed SPI-frame count |
| `0x35` | coherent I²S-domain RX level/high-water and TX level/high-water, four bits each |

The four I²S-domain sticky bits are safe to synchronize because they remain
asserted until an explicit clear. Their multibit FIFO level/high-water views use
the held-bus request/acknowledge capture and enter the retained image only after
the CDC transaction completes. A toggle-based command crossing converts one
fabric diagnostic-clear pulse into one I²S-clock pulse. Its unit test transfers
two separated events across unrelated clocks and explicitly shows that
destination reset with an odd retained source toggle replays the idempotent
command once. Ten formal properties hold through 40 arbitrary-clock steps when
each event waits for prior observation; structural synthesis is 1 LC / 5 FF.
This crossing is not a reset-independent or arbitrary-rate event channel.

## Initial register groups

| Group | Examples | Update rule |
|---|---|---|
| identity | core version, model ID/version, build hash | read-only |
| transport | mute request/status, sample-rate status, FIFO status | synchronized handshake |
| calibration | ADC volts/FS, DAC volts/FS, channel gain/offset | muted or atomic boundary |
| reference model | nominal asset selection only in V1 | state-reset transaction |
| variation | tube parameter set, component seed/tolerances | labeled variation mode; state-reset transaction |
| modern | subsonic enable, user volume | outside reference block; click-free ramp |
| diagnostics | counters, maxima, sticky fault bits | coherent snapshot/read-clear |

Write access to reference values is not a backdoor “tone control.” Arbitrary
experiments are creative mode and the active mode is included in captures.

The standalone stereo master-volume endpoint uses unsigned Q0.31 gain. Zero is
silence and `0x7fffffff` is deliberately treated as exact unity so reference
samples bypass multiplication bit-for-bit. Values with bit 31 set are rejected
with a sticky diagnostic. Each accepted target computes
`ceil(abs(target-current)/2^SLEW_SHIFT)` and moves by that fixed step only at
valid 48 kHz sample boundaries; the default shift of 10 reaches the target in
at most 1,024 samples (21.33 ms) without hardware division. The UI maps dB to
this linear target and serializes physical/touch/CEC/network requests. This
modern control belongs after the selected model and before the independent
safety-mute ramp.

The implemented calibration primitives consume positive signed-Q8.24
coefficients. ADC calibration is input-referred peak volts at PCM full scale;
DAC calibration is reciprocal peak volts. `calibration_commit_guard` now owns
the active pair in the pin-facing top. Its two active values reset to zero and
change together only when `update_valid` presents two positive candidates while
the downstream digital ramp reports muted. An accepted update produces a
one-clock acknowledgment. Invalid and live/unmuted attempts leave both active
values unchanged and set separate sticky diagnostics. The host must commit a
valid startup pair before releasing audio state; otherwise the arithmetic
blocks deliberately emit valid zero samples and flag invalid configuration.

This guard and its register bank are protocol-neutral and contain no hidden CDC
or coefficient slew. Bus requests must already be synchronous to the fabric
clock. Muted digital state makes the coefficient transition click-free at the
model boundary, but does not empty PCM already queued for the DAC. The
register-controlled pin wrapper supplies digital integration; queued-frame and
physical analog mute sequencing remain required.

The asynchronous audio FIFOs now expose local occupancy estimates and retained
high-water marks in all four owning-domain views (receive I²S/fabric and
transmit fabric/I²S). These values are derived from the local binary pointer and
the already synchronized remote Gray pointer. A write-side level may lag a read
high; a read-side level may lag a write low. They are intentionally raw-domain
diagnostics at their source. The two fabric views connect directly to the
snapshot image; `cdc_word_snapshot` captures the two I²S views coherently with a
four-phase request/acknowledge handshake, holds all 16 bits stable through two
synchronizer stages, and delays valid by a further clock. Existing domain-local
diagnostic clear inputs also reset the corresponding watermark to the current
projected occupancy.

Clock status now includes a fabric-domain measurement-valid pulse, last BCLK
edge count, consecutive-good-window count, live rate-lock flag, and sticky rate
error. The default monitor requires three 1,024 ± 1 edge windows. It is already
in the fabric domain and can enter the implemented coherent diagnostic snapshot
directly. Lock is live status; the sticky bit retains a bad window until the
fabric diagnostic clear. In the register-controlled wrapper, `!rate_locked` or
the retained rate error drives the modern immediate-mute input. Reacquiring
three good windows restores lock but cannot release audio until the host clears
the retained evidence. Snapshot word `0x20` bit 9 records that effective
rate-fault mute state; bit 18 remains the independent external force-mute pin.
The reduced-parameter formal instance proves 16 counter, CDC-pipeline, window,
lock/drop, and sticky-clear properties through 32 arbitrary-clock steps and
reaches lock followed by error. This is digital state-machine coverage; it does
not replace physical clock measurement or placed CDC analysis.

## Required counters

ADC/DAC clip, internal-node saturation, LUT out-of-range, solver residual failure,
iteration sum/max, deadline miss, FIFO under/overflow, invalid control commit,
and mute/fault events are saturating 32-bit counters. An overflowed diagnostic
counter remains all ones. Per-node maxima use physical Q formats and clear only
by explicit command. These semantics allow formal proofs of no wrap and atomic
snapshot behavior later.

SPI is the simplest board-control candidate; UART is useful for bring-up and an
embedded CPU/USB bridge may be layered above the same register transaction bus.
`spi_control_transport` now implements the first such bridge without generating
an SPI-derived fabric clock. Two-flop input synchronizers and fabric-domain edge
detection oversample mode-0 CS/SCLK/MOSI; MISO changes on observed falling edges.
Each CS-low transaction is exactly 80 bits, MSB first:

```text
request  = write[1] + word_address[7] + write_data[32]
response = status[8] + read_data[32]
```

Response-status bit 0 is the register-bus error. CS deassertion before all 80
bits latches a frame error; a missing bus reply before response shifting latches
underflow; completed-frame count saturates. The test uses 5 MHz SPI against a
100 MHz fabric model and drives eight complete reads/writes through the real
register bank and calibration guard, including bad-address status, a ten-bit
abort, a deliberately withheld reply, and diagnostic clear. The transport is
warning-free and synthesizes to 112 LC / 172 FF / no DSP or RAM. This is not a
placed SCLK-limit claim; the board constraint must preserve comfortable
oversampling margin.

`make formal-spi-control` additionally leaves all three raw SPI pins, register
response timing/data, and diagnostic clear arbitrary after reset. Eleven
properties cover synchronization, the bit-count bound and transition, exact
request decode, response-state exclusion, saturating completed count, frame
reset, and sticky precedence through 32 fabric clocks. A separate 100-step
trace reaches request, short-frame, and underflow evidence. This is bounded
digital safety evidence; the directed eight-frame test remains the full-frame
wire-order check, and placed SCLK timing/metastability are not proven.

`phono_i2s_spi_top` composes that transport with the complete pin-facing audio
hierarchy. Its warning-free integration test executes 15 actual SPI frames,
commits and reads back the converter calibration pair, demonstrates that a
retained snapshot cannot tear when `force_mute` changes, takes a second image,
captures a deliberately aborted frame, reads the snapshotted transport-frame
count, and transfers one diagnostic-clear event into the unrelated I²S clock
domain. With the fail-closed BCLK guard and coherent I²S snapshot, flattened XC7
structural synthesis is 19,719 estimated logic cells / 18,856 FF / 216 DSP48E1 /
8 RAMB18E1 + 1 RAMB36E1. There is still no named-part SCLK, CDC, I/O, or
98.304 MHz timing claim, and no physical host backend. No protocol-specific
state belongs in the audio solver.

## Host-side codec

`fpga_amp.host_control` is the dependency-free software definition of this ABI.
It encodes the request and dummy response clocks in exact wire byte order,
decodes status/data, rejects short transfers, reserved status bits, bus errors,
identity/ABI/capability mismatches, and invalid register ranges. A typed client
provides explicit-mute snapshot and clear commands plus guarded two-coefficient
calibration commit/poll/sequence verification. Snapshot calls poll busy and
require the saturating sequence to advance (or remain at its maximum value),
reporting FPGA timeout evidence instead of returning a stale image as new.
Every CONTROL operation requires
the intended mute level as an argument, avoiding a stale host cache that could
silently change bit 0.

Six unit tests use a deterministic fake full-duplex link to cover exact frame
bytes, reads/writes, malformed responses, bus errors, explicit mute ownership,
diagnostic bounds, accepted calibration, rejected calibration, and unsafe
preconditions. The caller supplies one `bytes -> bytes` transfer function, so a
future Linux `spidev`, USB bridge, or embedded implementation does not redefine
framing. No physical adapter backend or board transaction has been validated.
