birdybro/FPGA_Amp/docs/fixed_point.md

# Fixed-point contract

The first tube primitive uses quantity-specific formats. These are implementation formats, not physical-model claims.

| Quantity | Unit | Nominal table range | RTL format | Rounding | Out-of-range behavior |
|---|---:|---:|---:|---|---|
| `v_gk` | V | -5 to +1 | signed Q8.24 | input producer contract | clamp and assert `range_clipped` |
| `v_pk` | V | 0 to 400 | signed Q12.20 | input producer contract | clamp and assert `range_clipped` |
| LUT coordinate | index | table extent | unsigned Q16 | add half LSB before reciprocal-scale shift | saturate at final cell |
| `i_p` | A | 0 to about 18 mA | signed Q0.31 | nearest at table generation and each interpolation axis | positive saturated table entry |
| `i_g` | A | about -1 nA to 0.23 mA | signed Q0.31 | same as `i_p` | grid-axis clamp |

`i_p` is bilinearly interpolated from a 128 × 256 table. `i_g` is linearly interpolated from a 128-entry table. Both are generated by `scripts/generate_tube_lut.py` from the Koren equations. Coordinate mapping uses checked-in Q24 reciprocal constants; RTL contains no divider. Mapping uses 64-bit products and interpolation retains the full 49-bit signed product/sum before a rounded 16-bit right shift. Saturation at the physical table boundary replaces wraparound.

The primitive is single-issue, uses one synchronous read port per ROM, and asserts `valid` eight fabric clocks after accepting `ce`. At 96 MHz and a 768 kHz simulation rate, this occupies 8 of the available 125 clocks per tube-current evaluation.

The table itself contributes physical-model approximation error. Q-format, coordinate, and interpolation error are measured together against the analytical model; that number must not be presented as error against a real tube.

## Modern stereo master volume

The post-model master-volume target and active gain use unsigned Q0.31. Zero is
silence. `0x7fffffff` is an exact-unity sentinel and bypasses multiplication so
reference samples are bit-identical; it is intentionally treated as 1.0 even
though the ordinary Q0.31 interpretation is one LSB below unity. Bit 31 is
invalid and produces a sticky control diagnostic.

Each stereo Q8.24 sample multiplies the 32-bit zero-extended gain as a signed
32 x 32 operation. The complete signed 64-bit product is retained, then shifted
31 bits with symmetric round-to-nearest, ties away from zero. Since accepted
gain never exceeds unity, the result cannot exceed the input magnitude and no
wrap/saturation case is created. Zero and unity bypass the multiplier exactly.

On target commit, the step is

```text
ceil(abs(target - active_gain) / 2^SLEW_SHIFT)
```

using add-and-shift arithmetic. The active gain moves by that fixed step only at
valid sample boundaries and clamps to the target, so it reaches the target
within `2^SLEW_SHIFT` accepted samples. Default `SLEW_SHIFT=10` is at most 1,024
samples or 21.33 ms at 48 kHz. This is a modern output control, not part of the
physical tube circuit.

## Converter calibration boundary

I²S PCM24 codes are dimensionless; the V1 circuit boundary is physical volts in
signed Q8.24. `pcm24_to_q8_24.sv` implements

```text
input_q24 = round_symmetric(pcm24 * input_peak_volts_q24 / 2^23)
input_peak_volts = ADC_peak_volts / measured_analog_gain
```

The input coefficient is positive signed Q8.24 and represents input-referred
cartridge-terminal peak voltage at negative PCM full scale. It must reflect the
measured physical loading/front-end path; it must not compensate the frozen
circuit response. A full 24×32-bit product is retained. Symmetric nearest
rounding uses exact ties away from zero. The positive signed-32 coefficient and
signed-24 input prove that the result fits signed Q8.24 without a saturator.
Positive or negative PCM endpoints increment a saturating diagnostic counter.

`q8_24_to_pcm24.sv` implements

```text
pcm24 = sat24(round_symmetric(output_q24 * reciprocal_peak_q24 / 2^25))
reciprocal_peak = 1 / DAC_peak_volts
```

The reciprocal is positive signed Q8.24 per volt and is precomputed outside RTL;
there is no divider. The 32×32-bit product is retained in 64 bits before the
25-bit rounded shift. Exact positive full scale saturates by one PCM code because
signed PCM24 is asymmetric; exact negative full scale is representable. The
output saturation counter itself saturates at `0xffffffff`. Either block emits a
valid zero sample and sets `configuration_error_sticky` when its coefficient is
nonpositive, avoiding an uncalibrated high-level output.

Both directions have one fabric-clock latency and require coefficients to be
stable in the fabric domain for an accepted sample. Python coefficient helpers
and 4,159 exact vectors per direction define the bit contract. Warning-free XC7
structural synthesis reports 95 LC / 66 FF / 4 DSP48E1 for input and 86 LC / 58
FF / 4 DSP48E1 for output. These dynamic-coefficient costs are not a stereo
scheduling decision or a placed timing result.

An independent formal gate exhaustively covers arbitrary PCM24/Q8.24 samples,
signed 32-bit coefficients, valids, and diagnostic clears. Twelve properties
prove that every valid positive input coefficient leaves the rounded/shifted
product inside signed 32 bits before the explicit cast, that output conversion
clips exactly to `0x7fffff`/`0x800000`, and that registered output/hold, valid,
saturating counter, and sticky-error transitions are exact. Yosys 0.66 SAT
temporal induction closes at depth 2; a separate trace reaches endpoint,
saturation, and both invalid-configuration paths. This digital proof does not
validate the physical volts represented by board-specific coefficients.

## Factorized tube candidate

The improved candidate retains the Q8.24/Q12.20 voltage and Q0.31 current
interfaces, but evaluates three scalar tables in sequence:

| Function | Axis format/range | Value format | Entries |
|---|---|---|---:|
| `1/sqrt(Kvb+Vpk²)` | Q12.20, 0…400 V | unsigned Q0.32 value/slope-step | 512 |
| `softplus(Kp*z)/Kp` | signed Q2.30, -0.30…0.08 | unsigned Q0.32 value/slope-step | 1024 |
| `2*E1^Ex/Kg1` | Q12.20, 0…6 V | unsigned Q0.31 value/slope-step | 2048 |
| grid current | Q8.24, -5…+1 V | unsigned Q0.31 value | 1024 |

For endpoints `y0/y1`, derivative-times-axis-step values `m0/m1`, and Q0.16
fraction `t`, fixed Python defines the exact Horner sequence:

```text
d  = y1 - y0
c2 = 3*d - 2*m0 - m1
c3 = -2*d + m0 + m1
y  = round(round(round(c3*t) + c2)*t + m0)*t + y0
```

Each multiply is rounded back to the table format with add-half then arithmetic
shift. `z` is Q2.30 and `E1` is Q12.20. The linear grid-current table uses 1,024
entries; its exact fixed mapping measures 12.55 nA worst absolute error and
2.82 nA RMS in the nonnegative-grid conduction region. Plate-current evaluation
accepts `Vgk` from -8 to +1 V; the
independent grid-current table retains its -5 to +1 V axis and clamps more
negative inputs to the modeled leakage-floor entry. The transformed-coordinate,
`Vpk`, and `E1` guards remain independent, so an externally bounded pair can
still assert `range_clipped` if an internal factor leaves its table. Total raw
table storage is 262,144 bits. These formats are a bit-accurate Python contract.
The standalone RTL passes 4,110 exact randomized/directed vectors, including
independent-coordinate clip cases, at eight clocks. Proven table bounds allow
the Hermite coefficient and Horner states to remain signed 32-bit with full
49-bit products. Generic XC7 synthesis reports 1,496 estimated logic cells,
35 DSP48E1s, and 8 RAMB18E1 + 1 RAMB36E1. Selectable solver integration is exact for 512
persistent-state samples at the unchanged 126-clock latency. Its hierarchy is
9,148 logic cells, 108 DSP48E1s, and 8 RAMB18E1 + 1 RAMB36E1. The complete factorized stream
also matches 64 outputs / 1,024 nonlinear updates exactly and synthesizes to
14,290 logic cells, 156 DSP48E1s, and 8 RAMB18E1 + 1 RAMB36E1. Both implementations remain
named while wider equivalence testing is open.

The standalone `hermite_q16_pipeline` makes the same arithmetic boundaries an
explicit reusable contract. It performs the three Horner products over three
clocks with one selected multiplier input, retains the 49-bit product, and
wraps to signed 32 bits after every rounded shift/add exactly as the original
function. Synthetic full-range operands are therefore defined as well as the
physically bounded table values. It passes 4,096 exact vectors and preserves
the complete factorized-tube regression. Yosys infers two DSP48E1s rather than
the dependent combinational chain; named-part open routing reports 132.54 MHz
at the experimental `DEFAULT` grade. This kernel has not changed the current
eight-clock tube or 127-clock solver numerical/cycle contract.

The alternative `FixedLinearFactorizedKoren12AX7` deliberately inherits every
coordinate, physical-domain, current-format, and saturation rule, but calls the
existing rounded Q0.16 linear interpolation for three larger value-only
tables. The selected 1,024/8,192/4,096 table sizes plus the unchanged 1,024-
point grid branch consume 458,752 raw bits. A dense 100,000-point fixed probe
measures 47.49 nA worst error. Its matching RTL passes all 4,110 exact tube
vectors at eight clocks, 512 wide-solver states at 116 clocks, and 512 complete
trapezoidal/banked/terminal states at 127 clocks. It is selectable at elaboration
time and does not alter the default Hermite assets.

## Circuit-state chord candidate

The complete Python fixed candidate uses heterogeneous 32-bit voltage formats:

| Node | Unit | Format | Approximate signed range / LSB |
|---|---:|---:|---:|
| `g1`, `k1`, `g2`, `eq_low`, `k2` | V | Q8.24 | ±128 V / 59.6 nV |
| `p1`, `eq_pre`, `p2`, `out` | V | Q12.20 | ±2048 V / 0.954 µV |
| capacitor history | V | Q12.20 | ±2048 V / 0.954 µV |
| dynamic conductance matrix | S | signed Q0.47, 48 bit | ±1 S / 7.11 fS |
| KCL residual/RHS | A | signed Q4.44, 48 bit | ±8 A / 56.8 fA |
| chord inverse | Ω | signed Q17.1, 18 bit | ±65.536 kΩ / 0.5 Ω |
| chord correction residual | A | signed 25 bit, 30 fractional | ±15.625 mA / 0.931 nA |

Each conductance-voltage product is rounded once into Q4.44 before KCL
accumulation. Tube Q0.31 current is exactly extended by 13 bits. Before chord
correction, the high-resolution diagnostic residual is rounded/saturated to the
25-bit Q30 operand. Each correction uses nine native DSP-sized 18×25-bit
coefficient/residual products, a signed 48-bit accumulator, one documented
add-half/arithmetic shift into the destination node format, and 32-bit
saturation. Capacitor differences are rounded to Q12.20 only after the corrected
node vector is committed.

### 384 kHz candidate formats

The explicitly non-reference 8× candidate regenerates its trapezoidal
conductances, quiescent capacitor-current history, initial node/capacitor state,
and all five chord banks at 384 kHz. It does not reuse the 768 kHz assets. The
largest capacitor conductance is 50,800,603,796,739 Q0.47 (0.36096 S), which
still fits the established signed 48-bit conductance contract.

The lower-rate chord inverse spans -23,414 through +146,717 in Q17.1. The
positive endpoint exceeds signed 18-bit range, so this candidate uses a signed
19-bit coefficient and a 44-bit raw coefficient/residual product before exact
sign extension into the existing 48-bit accumulator. The established 768 kHz
bank remains signed 18 bit (-10,596 through +124,001). This is a measured
numerical-format difference, not a circuit-value change.

At 384 kHz, 1,024 randomized/boundary chord vectors distribute 204 or 205
cases across each of the five banks and match RTL exactly at 10 clocks,
including 109 saturating cases. Another 1,024 randomized/directed KCL vectors
match exactly at 11 clocks, including 989 deliberate current-saturation cases. A 512-sample
persistent full-circuit sequence matches all fixed-point states and outputs at
127 clocks, with a 4.565 nA maximum recorded preterminal residual and zero
saturation, LUT-clip, nonconvergence, or correction-fallback diagnostics. The
core therefore leaves 129 clocks of a 256-clock sample period at 98.304 MHz;
the 8× converter stream and its alias behavior remain separate open gates.

The compact correction was selected by a reproducible precision study. Against
the original Q17.15 × Q4.44 correction, Q17.1 × 25-bit-Q30 is -83.63 dB
normalized residual, 0.492 mV worst output error, and -0.00047 dB RMS gain error
on the multitone, with no saturation. This makes each correction multiply fit a
DSP48E1's 25×18 multiplier. Broader overload proof remains required.

`chord_corrector_v1.sv` implements this correction with nine parallel row
multipliers and one column per clock. It matches 1,024 generated vectors exactly,
including 18 forced-saturation vectors, and produces results ten clocks after an
idle start. `network_rhs_v1.sv` and `network_kcl_v1.sv` separately match 1,024
vectors each at 12 and 10 clocks; the KCL test contains 18 deliberate Q30
residual saturation cases. The KCL block accepts tube current later than its
start so matrix multiplication overlaps the serialized tube ROM work.

`v1_solver_mono.sv` composes those blocks with the tube primitive. It matches
512 sequential samples bit-for-bit for all nine node voltages, all ten capacitor
states, output, final residual, and cumulative diagnostic counters. Silence,
tones, multitone, bounded noise, and ±100 mV click stimuli are included. Measured
latency is 126 fabric clocks per 768 kHz sample.

Exactly three chord corrections execute per sample; the fixed model does not
exit early based on quantized residual. A 2 µA residual diagnostic limit is a
provisional bound derived above the 1.43 µA observed operating-region LUT error,
not a replacement for the float solver's 100 pA criterion. The multitone test
observes 0.342 µA maximum residual with no saturation or LUT range clips.

For 10 mV peak at 50 Hz + 10 mV at 1 kHz + 5 mV at 10 kHz, settled fixed output
is -57.87 dB normalized residual and +0.00988 dB RMS gain from analytical/full-
Newton float. Error decomposition shows the floating LUT circuit itself at
-56.14 dB versus analytical float, while Q-format plus three-pass chord is
-70.33 dB versus the floating LUT circuit. Thus LUT device resolution—not fixed
state arithmetic—is the dominant measured downstream approximation in this test.
That conclusion is stimulus-specific. A settled 5 mV/1 kHz test measures
-43.41 dB for floating LUT versus analytical, -37.24 dB for complete fixed
versus analytical, and only -34.58 dB for fixed versus the same-LUT floating
circuit. The corresponding fixed THD is 0.0733% versus 0.0191% analytical.
The low-level state/LUT interaction is therefore now a tracked accuracy defect;
the multitone result must not be generalized to all signals.

Generic hierarchical XC7 synthesis of the complete solver reports 8,024
estimated logic cells, 89 DSP48E1s, and 47 RAMB18E1s. The RHS and KCL engines
account for 10 and 54 DSP48E1s respectively; the correction uses nine and the
tube primitive 16. These are structural results only. No named-device timing,
routing, or 98.304 MHz closure is claimed.

With `USE_FACTORIZED_TUBE=1`, the identical scheduler and network arithmetic
match the factorized fixed model bit-for-bit for 512 samples at the same 126
clocks. Structural resources become 9,148 logic cells, 108 DSP48E1s, eight
RAMB18E1s, and one RAMB36E1. Relative to the 2-D hierarchy this saves 37
RAMB18-equivalents while adding 19 DSPs and 1,124 logic cells. Both modes remain
named and reproducible.

The uniform Q12.20 capacitor/output-state choice is now known to be inadequate
for long settling. In a one-second silence/click regression, a one-sample
100 mV click leaves the fixed output held near +35.655 mV; after the opposite
click it remains at -5.368 mV in the 0.9--1.0 s window while analytical output
is about 7.2 uV RMS. The 0.954 uV state LSB is too coarse for the per-sample
decay of the roughly 1.04 s output-coupling time constant. Because the frozen
state is a valid solution of the quantized companion equations, residual,
saturation, and range diagnostics all remain clear. This is an exposed
numerical-contract failure, not reference behavior. Wider internal output/
history formats and a branch-current capacitor stamp are under measured
evaluation; the current RTL has not been silently changed.

The first measured replacement candidate uses 40-bit node words: Q28 for the
three high-voltage nodes (`p1`, `eq_pre`, `p2`) and Q32 elsewhere, including
`out`. Capacitor history is Q30, retaining +/-512 V range, and capacitor KCL is
formed as one rounded `G * (Vnow - Vprevious)` branch current. Chord residuals
use Q30, Q34, and Q40 on passes one through three respectively; this keeps the
first pass's +/-3.906 mA range while resolving late sub-nanoampere corrections.
Tube lookup interfaces remain Q8.24/Q12.20, so this changes the numerical state
layer rather than the tube device approximation.

Each late-pass format is a requested maximum rather than an unsafe fixed shift.
The candidate selects the finest available schedule format that keeps all nine
signed 25-bit residual operands in range, recording every fallback and its
minimum format. Ordinary signals use the requested Q30/Q34/Q40 sequence. The
1.5 V burst falls back 729 times to no less than Q34, eliminating the 1,429
operand saturations observed with a fixed scale. Restricting fallback to these
three formats makes the scaling hardware bounded and auditable.

`chord_corrector_v1_wide.sv` implements the complete 40-bit correction. It uses
the same Q17.1 inverse and nine parallel 18x25 multipliers, applies explicit
constant shifts for Q30/Q34/Q40 into each node format, and saturates at signed
40-bit node boundaries. It matches 1,024 generated randomized and directed
vectors exactly, including 95 vectors with at least one forced output
saturation, at ten clocks. Generic XC7 synthesis reports 1,701 estimated logic
cells, 9 DSP48E1s, and no block RAM. An earlier arbitrary runtime shifter
synthesized to 5,531 cells and was rejected; that experiment did not change the
numerical formats.

The wide network uses the 41-bit measured bound of the static resistor Q0.47
matrix rather than carrying unused 48-bit sign extension into every multiply.
Capacitor Q0.47 conductances require 47 bits. `network_rhs_v1_wide.sv` adds only
the Q8.24 sampled input to the fixed Q4.44 sources in two clocks. The KCL block
uses nine parallel static-matrix products and one time-multiplexed capacitor
product: capacitors 0--8 overlap matrix columns 0--8 and capacitor 9 is included
in the finish expression. Node voltages are rounded to Q30 before subtracting
the corresponding Q30 history; the resulting branch difference is multiplied
and rounded once to Q4.44 exactly as in Python.

The branch-difference datapath is signed 44-bit Q30 and its conductance product
is signed 92 bits. These widths are required by the declared state formats,
not merely by nominal operation: capacitor 6 joins two signed-40 Q28 nodes, so
the exact converted difference can span almost +/-4096 V before subtracting a
signed-40 Q30 history spanning +/-512 V. A previous 43-bit/91-bit pair could
therefore wrap at legal interface values. Directed positive and negative
full-range vectors now exercise that branch in both backward-Euler and
trapezoidal KCL regressions.

RHS and KCL each match 1,024 vectors exactly. KCL coverage includes Q30/Q34/Q40,
48 global scale fallbacks, 18 true Q30 overflow vectors, and tube currents
arriving zero through eleven clocks after request. Its ordinary latency is ten
clocks; a tube current arriving after the ninth calculation clock stalls the
finish rather than using stale data. Generic XC7 synthesis is 31 logic cells /
4 DSP48E1s for RHS and 8,034 logic cells / 72 DSP48E1s for KCL, with no block
RAM.

`make arithmetic-bounds` independently propagates conservative integer
intervals over every declared input/state bit pattern and the frozen V1
constants. All 47 storage, product, rounding-bias, branch-current, serialized
sum, chord-correction, and tube-pin conversion checks pass. Tight cases consume
all 44 capacitor
difference bits and all 34 pre-shift cathode-sum bits. The worst conservative
trapezoidal KCL partial sum requires 57 of 63 bits, while its capacitor product
requires 89 of 92 bits. The report is regenerated at
`reference/results/wide_arithmetic_bounds.json`; the default regression now
reruns the proof so coefficient changes cannot silently invalidate it.

The tube cathode stamp also widens each signed-32 Q31 operand to 34 bits before
negation. The exact boundary `(-INT32_MIN) + (-INT32_MIN) = 2^32` needs all 34
bits; directed vectors exercise the boundary independently for both triodes.

Tube-pin voltage formation also keeps each rounded node conversion in 40 bits,
subtracts in 41 bits, and only then saturates to the signed-32 Q8.24/Q12.20
device interface. Full-range Vgk and Vpk differences do not fit that interface;
the old 32-bit subtraction could wrap a large positive differential negative.
Fixed Python applies the identical saturation and classifies it with tube-range
clipping. Since either saturated endpoint is far outside the frozen -5..+1 V
grid or 0..400 V plate domain, RTL exposes the event through the existing LUT
clip counter. A unit regression forces both positive and negative full-range
node combinations.

### Cutoff-Jacobian bank candidate

Residual instrumentation localizes the 1 V convergence failure to second-stage
cutoff rather than grid conduction: every failing backward-Euler sample has
previous-sample Vgk2 below approximately -2.75 V. The DC Jacobian retains the
quiescent tube transconductance there even though the physical device-current
derivative is collapsing. Adding iterations does not repair this within the
128-clock schedule.

`FixedWideStateBankedChordV1CircuitModel` instead selects a small inverse bank
once per sample from the previous Vgk2 and holds it for all three corrections.
The inverse matrices are generated from the same frozen circuit and Koren
derivatives at measured cutoff-arc Vgk/Vpk points. The baseline partition uses
two backward-Euler cutoff matrices plus nominal and four trapezoidal matrices
plus nominal. All remain
within the existing signed-18 Q17.1 coefficient interface, so the projected
serialized schedule stays at 116 clocks. The integration modes deliberately
use separate assets because sharing the two-entry backward-Euler partition left
309 trapezoidal failures.

In a 100 ms, 1 kHz campaign with a 5 ms burst, the initial bank reduces 1.0 V
residual failures from 1,122 to zero for backward Euler and from 1,107 to zero
for trapezoidal. Maximum residual becomes 1.887/1.874 uA, below the 2 uA gate,
with zero arithmetic saturation, tube-range clips, or scale fallbacks. Its
first 1.5 V result left 72 backward-Euler and 67 trapezoidal failures. A later
exact-intermediate audit
proved all 4,052 formerly reported range events were solely `Vgk < -5 V` while
the evaluated `Vpk`, transformed coordinate, and `E1` remained valid. Expanding
the plate-law acceptance bound to -8 V removes those false diagnostics without
changing current or audio; the -5 V grid-current lookup clamp is unchanged.
This improves the FPGA approximation only and does not change the physical
reference circuit.

The synthesizable solver latches the bank from the previous sample's stage-two
Vgk and holds it through all three corrections. A 9,216-sample, 1.0 V capture
per integration mode matches every fixed node, capacitor state, output,
residual, and cumulative diagnostic word exactly; every generated bank is
selected and latency remains 116 clocks. The expanded 1.5 V RTL capture is also
full-state exact and records zero range, arithmetic, or scale-fallback events.
That capture initially retained 57/53 residual misses before the selector
extension below. Full-Newton waveform error remains a separate acceptance
question before making the bank the default reference implementation.

A subsequent 100 ms full-Newton audit closes the burst-waveform question but
does not erase the recovery-state tradeoff. With Q8.24 input and no gain, DC,
or delay alignment, the 1.0 V raw burst residual improves from -53.45 to
-76.43 dB for backward Euler and from -53.65 to -76.79 dB for trapezoidal.
Every 20 mV--1.0 V banked burst is below the frozen -70 dB gate. In the final
10 ms, however, the trapezoidal bank has 0.538 mV raw RMS and 0.537 mV mean
error versus
48.0 uV for the nonconvergent-during-burst baseline; removing the mean leaves
-89.75 dB error. This is evidence of a small slow-state displacement, not
permission to DC-align the comparison, and keeps the bank optional.

A prefix-minimization sweep proves the offset cannot be addressed by merely
deleting the shallowest matrix. Retaining one of two backward-Euler cutoff
matrices leaves 289 residual failures at 1.0 V; retaining three of four
trapezoidal matrices leaves 119. All present coefficient sets therefore remain
required under the current thresholds.

The fourth trapezoidal cutoff matrix remains necessary, but its activation
threshold need not be -2.50 V. A sweep from -2.50 through -2.90 V finds -2.75 V
to be the most-negative tested threshold with zero 0.5/1.0 V failures. It
eliminates all 231 shallow-bank activations at 0.5 V, retains 154 at 1.0 V, and
halves the final-window mean error from 1.042 to 0.537 mV. At -2.80 V two
samples exceed the residual limit, so that more aggressive boundary is
rejected.

A separate selector study observes a clean slew separation on the shallow
cutoff arc. Across the tested 100 ms records, accepted 0.5/1.0 V trajectories
stay below 17.4 mV of absolute previous-Vgk change per 768 kHz sample, while
the failing 1.5 V samples exceed 23.3 mV. The implementation therefore enables
a shallow bank only when previous Vgk2 is below -2.50 V and its absolute
sample-to-sample change exceeds 20 mV. Backward Euler adds a matrix evaluated
at the (-2.25 V, 261 V) representative; trapezoidal reuses its fourth
cutoff matrix. The <=1.0 V output is bit-exact to the previous selector.

The production 100 ms gate reduces the 1.5 V failure counts from 72/67 to zero,
with maximum residual below 1.9 uA and no arithmetic, range, or scale event.
In the 12 ms RTL gate, all 36,864 states across 1.0/1.5 V and both integration
modes are exact, every generated bank is selected in aggregate, and latency
remains 116 clocks. Structural synthesis measures 13,302 logic cells / 120
DSP48E1 / 8 RAMB18E1 + 1 RAMB36E1 for backward Euler and 13,840 / 120 /
8 RAMB18E1 + 1 RAMB36E1 for trapezoidal.
No Fmax is claimed from the structural flow.

The first converged waveform gate used a 128-point linear grid-current table.
At 1.5 V its unaligned raw burst residual versus full Newton was
-61.80/-62.12 dB and final 10 ms RMS error was 18.26/17.36 mV for backward
Euler/trapezoidal. A layer decomposition and 128/256/512/1,024-point sweep
identified that branch as the severe recovery limit. The implemented
1,024-point table improves 1.5 V burst residual to -72.87/-81.77 dB and final
RMS error to 0.631/0.321 mV; at 1.0 V final RMS error is 0.372/0.291 mV. All
fixed diagnostics remain zero. The larger table adds 28,672 raw bits but no
mapped RAMB18E1 to the measured standalone or banked hierarchies.

A further A/B evaluates the same quantized table coefficients continuously at
the fixed Q24/Q20 input boundary, rounds only the resulting currents to Q31,
and runs that device through the unchanged banked fixed circuit. Relative to
that path, the production integer Hermite evaluator contributes 0.149--0.168 mV
RMS during the tested 1.0/1.5 V bursts. Fixed node, capacitor, and chord
arithmetic contributes 10.60/19.07 mV for backward Euler and 10.19/6.40 mV for
trapezoidal. All intermediate runs have zero residual-limit, saturation, range,
or correction-fallback events. The next numerical investigation therefore
targets circuit/state/chord arithmetic rather than the tube primitive.

Sweeping three through six banked corrections on the same 100 ms records shows
that pass truncation is a large part of the burst term. The fourth pass reduces
raw burst error by 5.65--9.02 dB across both modes and levels. Six passes leave
only 0.111--0.207 uA maximum residual and 2.35--2.94 mV burst RMS, but final
10 ms error is non-monotonic with pass count because each trajectory commits a
different capacitor state. The measured three-pass solver is 116 clocks; one
serialized 19-clock residual plus ten-clock correction projects the fourth pass
to 145 clocks. The backward-Euler terminal-correction mode avoids that extra
residual evaluation: it applies one Q40 chord correction to the diagnostic
residual already available after the third correction. The committed output and
capacitor voltage state are bit-exact to a conventional four-pass trajectory,
while `last_residual_q44` and `nonconvergence_count` deliberately describe the
preterminal state. Integrated backward-Euler RTL measures 127 clocks, leaving
one clock at 98.304 MHz / 768 kHz. The later trapezoidal terminal path
implements the corresponding corrected Q4.44 capacitor-current-history commit
and is verified separately below; the statement that this path was Python-only
was the initial candidate status, not the current implementation status.

The two tube sections can instead be evaluated concurrently because each is a
function of the same candidate node vector within a pass. A selectable RTL
schedule duplicates the exact factorized Hermite primitive and launches both
physical operating points on the same edge. The backward-Euler and complete
trapezoidal/terminal regressions remain bit-exact while latency falls from
116/127 to 84/95 clocks. This recovers 32 clocks for future KCL and chord
pipeline registers; it changes resource scheduling only, not a Q format,
physical equation, solver iteration, or reference-mode result.

The recovered schedule now has independently selectable, bit-exact register
boundaries in both circuit blocks. In each KCL call, `PIPELINED_COLUMNS`
overlaps nine product issues, product rounding, and prior-column accumulation
with two fill clocks, while `PIPELINED_FINISH` separates physical-residual
capture, Q30/Q34/Q40 conversion, global fallback/diagnostic reduction, and
output saturation with two more clocks. `PIPELINED_CHORD_APPLY` separates
correction scaling, node subtraction/diagnostics, and saturation commit with
two clocks per correction. With parallel tubes and all three schedules, the
complete four-correction trapezoidal terminal solver is bit-exact across 512
stateful vectors at 119 clocks, leaving nine of 128 clocks. The optional KCL
unit is exact across 1,024 backward-Euler and 1,024 trapezoidal vectors at 15
early-current clocks; the optional chord unit is exact across 1,024 vectors at
12 clocks. These registers alter only scheduling, not formats, rounding,
saturation, model coefficients, or the frozen physical circuit.

Route extraction then showed that the exact nine-row maximum diagnostic, not
the physical accumulator, limited this 15-clock KCL. `PIPELINED_ACCUMULATOR`
registers matrix-current plus capacitor-stamp before its feedback addition;
`PIPELINED_MAXIMUM` reduces the final pass's maximum through four registered
single-comparator levels. The solver asserts that extra maximum schedule only
for the residual it actually reports. Earlier residual passes do not consume
the maximum and bypass its three clocks. The resulting complete solver is
bit-exact across the same 512 vectors at 126 clocks, while a diagnostic-enabled
standalone KCL is exact across 1,024 vectors per integration mode at 19 clocks.

The signed 25-bit overflow predicate is implemented as an exact sign-extension
test: a converted value fits when bits 62:25 all equal bit 24. Q34 and Q40 can
be selected only after their all-row fit test, so their selected saturation
count is necessarily zero; the only counted fallback is the registered Q30
vector. The unit regression retains all 48 fallback vectors and 18 deliberate
correction-saturation vectors. This source formulation reduces the selected
open-flow KCL netlist to 29,514 packed LUT elements and improves legal routed
timing from 64.90 to 92.23 MHz without changing any numerical result. The
98.304 MHz target and full-solver route remain open.

The backward-Euler terminal contract is also integrated in the bit-accurate
48→768→48 kHz composition. A 64-output regression covers 1,024 internal circuit
updates and matches RTL exactly at 127 clocks per solve with zero conversion,
resampler, range, convergence, saturation, or deadline events.

Across 100 ms 1.0/1.5 V backward-Euler bursts, terminal reuse reduces raw burst
RMS from 10.829/19.251 mV to 4.895/6.817 mV and remains diagnostic-clean. A
separate 18,432-sample RTL campaign exercises every bank and matches Python at
every persistent state and diagnostic word. This is an optional FPGA numerical
implementation choice; it changes neither the frozen physical circuit nor the
analytical tube equations.

Three schedule-neutral trapezoidal follow-up studies reject simpler ways to
reduce the remaining 4.709/3.604 mV burst term. Reselecting the existing bank
from the corrected state before the terminal update improves the 1.0 V burst
to 4.611 mV, but worsens the 1.5 V burst to 3.647 mV and both late-recovery
windows. Reselecting after every correction is worse still at 1.5 V. Scaling
the already available terminal residual by 5/4 improves the two burst windows
to 3.570/3.454 mV, but increases final-window error from 0.036/0.461 mV to
0.135/0.504 mV. Limiting that scale to cutoff-bank samples does not isolate the
benefit: 5/4 produces 4.749/3.700 mV burst and 0.393/1.091 mV final error. The
state committed by even a short conditional correction persists after its
selector condition ends.

Replacing the four cutoff matrices with Jacobians evaluated at both triodes'
full-Newton median operating points also fails cross-level validation. The best
1.0 V-derived unsplit set gives 4.645 mV at 1.0 V but 3.689 mV at 1.5 V and
raises the 1.0 V final error to 0.577 mV. Splitting every stage-two cutoff bank
again by stage-one Vgk adds eight physical Jacobian points but creates 58
preterminal residual-limit misses at 1.5 V and raises its burst error to about
6.12 mV. These are recorded negative numerical experiments, not production
changes. The implemented stage-two-only held bank, unity terminal correction,
127-clock schedule, and frozen physical reference therefore remain unchanged.

A longer captured RTL campaign covers a nominal control plus 20 mV, 0.5 V,
1.0 V, and 1.5 V five-cycle bursts, totaling 384,000 updates. Every node,
capacitor state, output, and diagnostic matches fixed Python. Direct analytical
burst RMS errors are 0.288, 1.237, 4.895, and 6.817 mV. The final-three-cycle
H2--H10 ratios are 0.903%, 3.274%, 10.928%, and 25.213%; their RTL/analytical
difference stays within 0.00122 percentage points and fundamental phase within
0.00221 degrees. The window includes physical burst transients and is therefore
not claimed as settled continuous-drive THD.

`v1_solver_mono_wide.sv` composes those blocks with the factorized tube and
matches 512 sequential fixed-Python samples exactly across all nine nodes, ten
capacitor histories, output, residual, and cumulative diagnostics. The vector
set covers silence, tone, multitone, bounded noise, and bipolar 100 mV clicks.
The scheduler passes Q30, Q34, and Q40 in the intended order; a regression found
and fixed an initial handoff bug that had latched the previous pass's format.
Measured latency is 116 clocks, leaving 12 clocks at 98.304 MHz / 768 kHz.
Hierarchical synthesis reports 12,544 logic cells, 120 DSP48E1s, eight
RAMB18E1s, and one RAMB36E1 with zero structural check problems. This
establishes numerical and cycle equivalence, not placed timing closure.

The complete wide stream rounds solver Q8.32 output to external Q8.24 using the
same add-half/arithmetic-shift rule before the existing bit-accurate decimator.
It matches 64 fixed-composition outputs spanning 1,024 solver updates exactly,
with zero rate-converter, numerical, LUT, convergence, deadline, or fallback
events and a maximum 4.598 nA residual. Generic XC7 synthesis reports 17,492
logic cells, 168 DSP48E1s, and 8 RAMB18E1 + 1 RAMB36E1. This is now the best-accuracy
complete RTL path, while the legacy modes remain reproducible for comparison.

On the same 768,000-sample bipolar-click audit, late raw output residual falls
from 5.375 mV RMS to 38.74 uV RMS and between-click residual falls from
36.09 mV to 0.358 mV. Maximum fixed KCL residual falls from 0.334 uA to
5.01 nA with zero diagnostic events. At 5 mV/1 kHz, raw null improves from
-42.90 to -63.83 dB, phase error from +0.00958 to -0.00019 degrees, and gain
error from +0.000257 to -0.000058 dB. Candidate THD is 0.01937% versus
0.01906% analytical. This is a successful architecture candidate whose complete
factorized solver now has bit-exact RTL and structural resource and cycle
measurements. Float/SPICE error remains separately characterized above.

The six-point 5 mV sweep bounds the wide candidate to 0.000196 dB gain error
and 0.000982 degrees phase error from 20 Hz through 20 kHz, with zero residual,
saturation, or tube-range events across 683,520 samples. Raw residual is
-95.26 dB at 20 Hz and -44.75 dB at 20 kHz; the latter remains dominated by a
-0.234 mV mean difference relative to the small RIAA-attenuated output, while
the 20 kHz mean-removed null is -68.37 dB. Frequency behavior passes the Python
gate; overload and hardware scheduling remain open.

The trapezoidal extension preserves the same node and Q30 voltage-history
formats and adds one signed 48-bit Q4.44 current-history word per capacitor.
For each branch it evaluates and commits exactly

```text
i[n] = round_Q4.44((2*C/dt) * (v[n] - v[n-1])) - i[n-1]
```

The same rounded expression is stamped into KCL, avoiding a model/commit
mismatch. All current histories reset to zero at the quantized DC operating
point. In the six-point 5 mV sweep, the largest stored-current magnitude is
2.25 uA, and fixed-versus-floating trapezoidal gain/phase error remains within
0.000131 dB / 0.000784 degrees with zero fixed diagnostics. Q4.44 deliberately
retains the existing residual-current resolution; large-signal range and RTL
storage/schedule costs are not yet accepted.

The overload sweep measures a 203.34 uA maximum stored branch current through
1.5 V peak input, still far inside signed Q4.44. No current-state saturation is
observed. Coefficient reuse is not width-neutral, however: the 470 nF output
coupling capacitor changes from 0.36096 S to 0.72192 S. Its Q0.47 integer is
101601207593478, requiring 48 signed bits rather than the 47-bit backward-Euler
capacitor-coefficient contract. Any trapezoidal RTL must widen that coefficient
and its multiplier input explicitly.

`network_kcl_v1_wide.sv` now performs that widening behind an explicit
`TRAPEZOIDAL` parameter. It latches ten signed Q4.44 previous-current inputs,
subtracts them in the corresponding branch stamps, and returns ten saturated
Q4.44 currents for commit. The existing column schedule remains ten clocks.
An independent 1,024-vector regression is exact for residuals, selected
correction format, maximum residual, all current states, and both saturation
counts; 1,013 intentionally extreme vectors exercise current saturation. The
default backward-Euler mode still passes its original 1,024 vectors exactly.

The persistent solver selects a separate Q17.1 chord-inverse ROM because the
trapezoidal companion conductances change the quiescent Jacobian. A regression
that initially reused the backward-Euler inverse failed on sample zero and is
now prevented by explicit integration-mode assets. With the matched inverse,
RTL equals fixed Python across 512 sequential samples at all nine nodes, ten
Q30 voltage histories, ten Q4.44 current histories, and every diagnostic. The
latency remains 116 clocks. Generic XC7 synthesis is 12,786 estimated logic
cells, 120 DSP48E1s, and 8 RAMB18E1 + 1 RAMB36E1, versus 12,544 / 120 /
8 RAMB18E1 + 1 RAMB36E1 for backward Euler. No Fmax is inferred from structural
synthesis.

The complete selectable 48 kHz path retains the established Q8.24 boundary and
Q8.32-to-Q8.24 output rounding. It matches fixed Python for 64 outputs spanning
1,024 internal circuit updates with zero diagnostic events and 5.02 nA maximum
residual. Structural synthesis measures 17,735 logic cells, 168 DSP48E1s, and
8 RAMB18E1 + 1 RAMB36E1, versus 17,492 / 168 / 8 RAMB18E1 + 1 RAMB36E1 for
backward Euler. The 243-cell delta is measured; timing closure remains unproven.

The optional terminal chord now supports trapezoidal state without a serialized
history pass. On the final chord-valid edge, RTL derives each saturated Q30
branch voltage, evaluates `G*(v[n]-v[n-1])-i[n-1]` in Q4.44 with the same
positive-half-LSB rounding as fixed Python, and saturates ten signed 48-bit
histories. All 512 nominal samples and 384,000 overload updates match every
fixed node and capacitor state at 127 clocks. Generated frozen-V1 conductance
constants let Yosys reduce the parallel products. The current controlled build
measures 13,158 logic cells / 174 DSP48E1s / 8 RAMB18E1 + 1 RAMB36E1 for the
solver and 18,302 / 222 / 8 RAMB18E1 + 1 RAMB36E1 for the initial complete
768 kHz stream. Serializing the decimator center tap through its existing MAC
first superseded those complete-stream counts with 18,280 / 206 and 17,693 /
207 at 768/384 kHz. Replacing the shifting decimator histories with reset-
masked circular distributed memory in both resamplers then reduces the 384 kHz
stream to 15,716 LC / 8,547 FF / 207 DSP and the 768 kHz stream to 16,062 /
9,033 / 206, with the same block RAM. A200T heap placement now legalizes;
static placement reaches only 41.27 MHz against 49.152 MHz, so
structural and placement success are not misstated as timing closure.

The overload gate passes only through the measured 0.5 V level. At 20 mV, the
candidate matches analytical 10%/1% recovery within about 0.002/0.000 ms and
reduces post-burst fixed/analytical RMS from 5.80 mV legacy to 0.258 mV. At
0.5 V its maximum residual is 0.351 uA with zero diagnostics. At 1.0/1.5 V it
still records 1,122/1,695 residual-limit failures; the latter retains 4,046 tube
range clips. Adaptive scaling prevents arithmetic saturation but is not a
nonlinear solver fix.
