birdybro/FPGA_Amp/rtl/io/audio_frame_scheduler.sv

`timescale 1ns/1ps
`default_nettype none

// Align held ready/valid stereo frames to a deterministic fabric-clock phase.
// The output is combinational during exactly one launch clock. A registered
// preprocessing block of PREPROCESS_LATENCY_CLOCKS then presents its valid at
// phase zero to a consumer reset from the same rst_n.
module audio_frame_scheduler #(
    parameter int unsigned PERIOD_CLOCKS = 2048,
    parameter int unsigned PREPROCESS_LATENCY_CLOCKS = 1
) (
    input  logic                 clk,
    input  logic                 rst_n,
    input  logic [63:0]          frame_input_data,
    input  logic                 frame_input_valid,
    output logic                 frame_input_ready,
    output logic [63:0]          frame_output_data,
    output logic                 frame_output_valid,
    output logic                 frame_was_present,
    input  logic                 clear_diagnostics,
    output logic [31:0]          underflow_count,
    output logic [$clog2(PERIOD_CLOCKS)-1:0] phase_counter
);

    localparam int unsigned PHASE_WIDTH = $clog2(PERIOD_CLOCKS);
    localparam logic [PHASE_WIDTH-1:0] LAST_PHASE =
        PHASE_WIDTH'(PERIOD_CLOCKS - 1);
    localparam logic [PHASE_WIDTH-1:0] LAUNCH_PHASE =
        PHASE_WIDTH'(PERIOD_CLOCKS - PREPROCESS_LATENCY_CLOCKS);
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
